wez/halfdeck/case/left-case.scad

module quarter(x, y, z, y_cut_delta=0, x_cut_delta=0, offset=[0,0,0], piece) {
    tongue_size = 2.8;
    displacement = 12;
    // tolerance on the groove side
    kerf = 0.25;

    y_cut = (y / 2) + y_cut_delta;
    x_cut = (x / 2) + x_cut_delta;
    total_z = z * 2;

    module cutout(kerf=0) {
        rotate([90, 0, 0])
        cylinder(h=kerf + max(y + abs(y_cut_delta),
                              x + abs(x_cut_delta))/2,
                 r=tongue_size, $fn=4);
    }

    module tongue() {
        cutout();
    }

    module groove() {
        cutout(kerf);
    }

    module top_left_quadrant() {
        cube([x_cut, y_cut, total_z]);
    }

    module offset_top_right() {
        translate([x_cut, 0, 0]) children();
    }

    module top_right_quadrant() {
        offset_top_right()
        cube([x - x_cut, y_cut, total_z]);
    }

    module offset_bottom_left() {
        translate([0, y_cut, 0]) children();
    }

    module bottom_left_quadrant() {
        offset_bottom_left()
        cube([x_cut, y - y_cut, total_z]);
    }

    module offset_bottom_right() {
        translate([x_cut, y_cut, 0]) children();
    }

    module bottom_right_quadrant() {
        offset_bottom_right()
        cube([x - x_cut, y - y_cut, total_z]);
    }

    module offset_top_left_lr() {
      offset_top_right()
      translate([0, y_cut, z/2])
      children();
    }

    module offset_bottom_left_lr() {
      offset_bottom_left()
      translate([x - x_cut, y - y_cut, z/2])
      children();
    }

    module offset_top_left_ud() {
      translate([0, y_cut, z/2])
      rotate([0, 0, 90])
      children();
    }

    module offset_top_right_ud() {
      offset_bottom_right()
      translate([0, 0, z/2])
      rotate([0, 0, 90])
      children();
    }

    // top left quadrant
    if (piece == undef || piece == 0)
    translate([-displacement, -displacement, 0]) {
      intersection() {
        translate(offset) {
          difference() {
            union() {
              top_left_quadrant();
              // RHS tongue
              intersection() {
                top_right_quadrant();
                offset_top_left_lr() tongue();
              }
            }
            // bottom groove
            offset_top_left_ud() groove();
          }
        }
        children(0);
      }
    }

    // top right quadrant
    if (piece == undef || piece == 1)
    translate([displacement, -displacement, 0]) {
      intersection() {
        translate(offset) {
          difference() {
            union() {
              top_right_quadrant();
              // bottom tongue
              intersection() {
                bottom_right_quadrant();
                offset_top_right_ud() tongue();
              }
            }
            // LHS groove
            offset_top_left_lr() groove();
          }
        }
        children(0);
      }
    }

    // bottom right quadrant
    if (piece == undef || piece == 2)
    translate([displacement, displacement, 0]) {
      intersection() {
        translate(offset) {
          difference() {
            union() {
              bottom_right_quadrant();
              // LHS tongue
              intersection() {
                bottom_left_quadrant();
                offset_bottom_left_lr() tongue();
              }
            }
            // top groove
            offset_top_right_ud() groove();
          }
        }
        children(0);
      }
    }

    // bottom left quadrant
    if (piece == undef || piece == 3)
    translate([-displacement, displacement, 0]) {
      intersection() {
        translate(offset) {
          difference() {
            union() {
              bottom_left_quadrant();
              // top tongue
              intersection() {
                top_left_quadrant();
                offset_top_left_ud() tongue();
              }
            }
            // RHS groove
            offset_bottom_left_lr() groove();
          }
        }
        children(0);
      }
    }
}


module case_top() {
difference() {
difference() {
difference() {
union() {
union() {
union() {
union() {
linear_extrude(height=2.0) {
polygon([
  [119.9620436791635, -10.0],
  [119.88614853201763, -9.998847719777999],
  [53.880686985647216, -7.994126032720432],
  [53.646495296320076, -7.975973004726603],
  [-5.810086836473021, -0.5439002381274649],
  [-6.047487665291121, -0.5025204617148387],
  [-6.279801550623147, -0.4384759607689326],
  [-6.504869964194179, -0.3523618003068363],
  [-6.720601698525187, -0.2449781040489396],
  [-6.9249922972416, -0.11732262012514494],
  [-7.116142679340018, 0.029418549432351115],
  [-7.292276784366992, 0.19388196927341883],
  [-7.451758074560958, 0.3745395389945354],
  [-7.593104740628792, 0.569712691377185],
  [-7.71500346987358, 0.7775879886781831],
  [-7.816321648748018, 0.9962339720600868],
  [-7.896117886454252, 1.2236191076063734],
  [-7.953650761810862, 1.45763066217724],
  [-7.988385712116106, 1.69609433372233],
  [-8.0, 1.9367944536567043],
  [-8.000000000000002, 99.39375],
  [-7.999999999999999, 126.83538329329558],
  [-7.988630737664156, 127.07353671349598],
  [-7.954626358757477, 127.30952403072804],
  [-7.898296147043448, 127.54119884361772],
  [-7.820152448885596, 127.76645397478553],
  [-7.720906013247321, 127.98324063648849],
  [-7.601459527138758, 128.18958706518433],
  [-7.462899405308439, 128.38361645552916],
  [-7.306485908855863, 128.56356403069117],
  [-7.133641682640258, 128.72779309371944],
  [-6.945938815742489, 128.87480991397337],
  [-6.745084542670518, 129.00327731321514],
  [-6.532905715361807, 129.11202682779387],
  [-6.311332187216184, 129.2000693363015],
  [-6.082379260288182, 129.26660405603724],
  [-5.848129355288844, 129.31102582645462],
  [-5.610713071115836, 129.33293061334462],
  [143.51094867944454, 135.94330272112006],
  [143.7578335033689, 135.94204409706296],
  [144.00339029973705, 135.9164401876724],
  [144.2452242532848, 135.86674069743202],
  [144.48097685611515, 135.79343032519606],
  [144.70834890926406, 135.69722403711918],
  [144.9251229458497, 135.57906009388333],
  [145.1291848571225, 135.44009090022388],
  [145.3185445105055, 135.2816717659965],
  [145.49135515854522, 135.10534768839287],
  [145.6459314494865, 134.91283828421348],
  [145.78076586382062, 134.70602101914633],
  [145.89454341650796, 134.48691289761004],
  [145.98615448149076, 134.25765079173254],
  [146.05470561342344, 134.02047060130883],
  [165.9330438628631, 49.86597310114771],
  [165.98320454827606, 49.58055907861434],
  [166.00000000000003, 49.291257900909926],
  [166.0, -6.398002531138397],
  [165.98859115294965, -6.63656923766047],
  [165.95446874123138, -6.872958527329727],
  [165.89794420274623, -7.105012856746026],
  [165.81953344134553, -7.3306142480280165],
  [165.7199521181364, -7.5477036197617124],
  [165.60010911958736, -7.754299580396419],
  [165.46109826205074, -7.9485165125592525],
  [165.30418830841614, -8.128581783231304],
  [165.13081138801294, -8.29285192270683],
  [164.9425499254547, -8.439827624668856],
  [164.7411221977268, -8.56816743047434],
  [164.52836665133918, -8.676699972751353],
  [164.3062251226821, -8.764434666560037],
  [164.07672511473476, -8.830570750538252],
  [163.8419612918881, -8.874504595512704],
  [163.60407636178044, -8.895835213869276],
  [137.156137109102, -9.99783268273088],
  [137.05206074732155, -10.0],
  [119.9620436791635, -10.0],
  [127.08639692372063, 86.55199944613877],
  [145.84698461860322, 89.85999723069379],
  [142.5389868340482, 108.62058492557635],
  [139.23098904949316, 127.38117262045891],
  [120.4704013546106, 124.07317483590388],
  [101.70981365972804, 120.76517705134886],
  [105.01781144428307, 102.00458935646631],
  [108.32580922883807, 83.24400166158375],
  [127.08639692372063, 86.55199944613877],
  [127.08639692372063, 86.55199944613877],
  [130.39439470827566, 67.7914117512562],
  [149.15498240315824, 71.09940953581122],
  [145.84698461860322, 89.85999723069378],
  [127.08639692372063, 86.55199944613877],
  [114.30000000000001, 26.19375],
  [114.30000000000001, 7.143750000000001],
  [133.35000000000002, 7.143750000000001],
  [133.35000000000002, 26.19375],
  [133.35000000000002, 45.24375],
  [133.35000000000002, 45.243750000000006],
  [133.35000000000002, 64.29375],
  [114.30000000000001, 64.29375],
  [114.30000000000001, 45.243750000000006],
  [114.30000000000001, 45.24375],
  [114.30000000000001, 26.19375],
  [0.0, 26.19375],
  [0.0, 7.143750000000001],
  [19.05, 7.143750000000001],
  [38.1, 7.143750000000001],
  [38.1, 2.38125],
  [57.150000000000006, 2.38125],
  [57.150000000000006, 0.0],
  [76.2, 0.0],
  [76.2, 2.38125],
  [95.25, 2.38125],
  [95.25, 4.7625],
  [114.3, 4.7625],
  [114.3, 23.8125],
  [114.3, 42.8625],
  [95.25, 42.8625],
  [95.25, 42.862500000000004],
  [114.3, 42.862500000000004],
  [114.3, 61.9125],
  [114.3, 61.91250000000001],
  [114.3, 80.9625],
  [95.25, 80.9625],
  [95.25, 78.58125],
  [76.2, 78.58125],
  [76.2, 76.2],
  [57.150000000000006, 76.2],
  [57.150000000000006, 78.58125],
  [38.1, 78.58125],
  [38.1, 83.34375],
  [38.1, 102.39375],
  [57.150000000000006, 102.39375],
  [57.150000000000006, 121.44375],
  [38.1, 121.44375],
  [19.05, 121.44375],
  [0.0, 121.44375],
  [0.0, 102.39375],
  [19.05, 102.39375],
  [19.05, 83.34375],
  [0.0, 83.34375],
  [0.0, 64.29375],
  [0.0, 45.243750000000006],
  [0.0, 45.24375],
  [0.0, 26.19375]
  ], [
  [
  0,
  1,
  2,
  3,
  4,
  5,
  6,
  7,
  8,
  9,
  10,
  11,
  12,
  13,
  14,
  15,
  16,
  17,
  18,
  19,
  20,
  21,
  22,
  23,
  24,
  25,
  26,
  27,
  28,
  29,
  30,
  31,
  32,
  33,
  34,
  35,
  36,
  37,
  38,
  39,
  40,
  41,
  42,
  43,
  44,
  45,
  46,
  47,
  48,
  49,
  50,
  51,
  52,
  53,
  54,
  55,
  56,
  57,
  58,
  59,
  60,
  61,
  62,
  63,
  64,
  65,
  66,
  67,
  68,
  69,
  70,
  71,
  72,
  73,
  74,
  75
  ],
  [
  76,
  77,
  78,
  79,
  80,
  81,
  82,
  83,
  84
  ],
  [
  85,
  86,
  87,
  88,
  89
  ],
  [
  90,
  91,
  92,
  93,
  94,
  95,
  96,
  97,
  98,
  99,
  100
  ],
  [
  101,
  102,
  103,
  104,
  105,
  106,
  107,
  108,
  109,
  110,
  111,
  112,
  113,
  114,
  115,
  116,
  117,
  118,
  119,
  120,
  121,
  122,
  123,
  124,
  125,
  126,
  127,
  128,
  129,
  130,
  131,
  132,
  133,
  134,
  135,
  136,
  137,
  138,
  139,
  140,
  141,
  142
  ]
  ]);

}
translate(v=[0, 0, 1.0]) {
linear_extrude(height=11.4) {
union() {
union() {
union() {
union() {
union() {
union() {
union() {
polygon([
  [56.956582132793095, -5.495278312942434],
  [56.94213631280969, -5.789329733931115],
  [56.898937974002784, -6.0805492789908175],
  [56.82740313998972, -6.36613234470582],
  [56.72822073032695, -6.643328610037702],
  [56.60234592583816, -6.909468523420426],
  [56.45099096970073, -7.161989012001239],
  [56.275613492881305, -7.398458165433368],
  [56.07790247635274, -7.616598656502074],
  [55.85976198528403, -7.8143096730306425],
  [55.623292831851906, -7.9896871498500674],
  [55.37077234327109, -8.141042105987497],
  [55.10463242988837, -8.266916910476294],
  [54.82743616455649, -8.366099320139059],
  [54.541853098841486, -8.437634154152125],
  [54.25063355378178, -8.480832492959024],
  [53.9565821327931, -8.495278312942434],
  [53.662530711804415, -8.480832492959024],
  [53.37131116674472, -8.437634154152125],
  [53.085728101029716, -8.366099320139062],
  [52.808531835697835, -8.266916910476297],
  [52.542391922315105, -8.141042105987502],
  [52.28987143373429, -7.989687149850073],
  [52.053402280302166, -7.814309673030648],
  [51.835261789233456, -7.61659865650208],
  [51.637550772704884, -7.398458165433374],
  [51.462173295885464, -7.161989012001245],
  [51.31081833974803, -6.909468523420431],
  [51.18494353525924, -6.643328610037707],
  [51.08576112559647, -6.366132344705825],
  [51.014226291583405, -6.080549278990822],
  [50.9710279527765, -5.789329733931119],
  [50.956582132793095, -5.495278312942436],
  [50.9710279527765, -5.2012268919537545],
  [51.014226291583405, -4.9100073468940515],
  [51.08576112559647, -4.624424281179048],
  [51.18494353525924, -4.347228015847166],
  [51.31081833974803, -4.081088102464442],
  [51.46217329588546, -3.828567613883628],
  [51.637550772704884, -3.592098460451498],
  [51.83526178923345, -3.3739579693827912],
  [52.05340228030216, -3.176246952854224],
  [52.289871433734284, -3.0008694760347994],
  [52.5423919223151, -2.84951451989737],
  [52.80853183569782, -2.723639715408575],
  [53.0857281010297, -2.6244573057458087],
  [53.371311166744704, -2.5529224717327437],
  [53.66253071180441, -2.509724132925844],
  [53.95658213279309, -2.4952783129424336],
  [54.25063355378177, -2.509724132925842],
  [54.54185309884147, -2.5529224717327406],
  [54.827436164556474, -2.624457305745804],
  [55.104632429888355, -2.7236397154085683],
  [55.37077234327108, -2.849514519897362],
  [55.62329283185189, -3.00086947603479],
  [55.85976198528402, -3.176246952854213],
  [56.077902476352726, -3.3739579693827793],
  [56.27561349288129, -3.5920984604514836],
  [56.45099096970072, -3.8285676138836116],
  [56.60234592583815, -4.081088102464424],
  [56.728220730326946, -4.347228015847145],
  [56.82740313998971, -4.624424281179026],
  [56.898937974002784, -4.910007346894027],
  [56.94213631280968, -5.201226891953728],
  [56.956582132793095, -5.495278312942409],
  [56.956582132793095, -5.495278312942434]
  ], [
  [
  0,
  1,
  2,
  3,
  4,
  5,
  6,
  7,
  8,
  9,
  10,
  11,
  12,
  13,
  14,
  15,
  16,
  17,
  18,
  19,
  20,
  21,
  22,
  23,
  24,
  25,
  26,
  27,
  28,
  29,
  30,
  31,
  32,
  33,
  34,
  35,
  36,
  37,
  38,
  39,
  40,
  41,
  42,
  43,
  44,
  45,
  46,
  47,
  48,
  49,
  50,
  51,
  52,
  53,
  54,
  55,
  56,
  57,
  58,
  59,
  60,
  61,
  62,
  63,
  64,
  65
  ]
  ]);

polygon([
  [-2.5, 1.9367944536567043],
  [-2.5144458199834094, 1.6427430326680228],
  [-2.5576441587903083, 1.3515234876083202],
  [-2.6291789928033733, 1.065940421893318],
  [-2.728361402466139, 0.7887441565614361],
  [-2.8542362069549343, 0.5226042431787128],
  [-3.0055911630923635, 0.27008375459789913],
  [-3.1809686399117876, 0.03361460116576942],
  [-3.3786796564403554, -0.18452588990293628],
  [-3.596820147509061, -0.38223690643150454],
  [-3.833289300941191, -0.5576143832509295],
  [-4.0858097895220045, -0.7089693393883592],
  [-4.351949702904728, -0.8348441438771548],
  [-4.629145968236609, -0.934026553539921],
  [-4.914729033951611, -1.005561387552986],
  [-5.205948579011314, -1.0487597263598858],
  [-5.499999999999996, -1.0632055463432957],
  [-5.794051420988676, -1.0487597263598867],
  [-6.0852709660483795, -1.0055613875529879],
  [-6.370854031763382, -0.9340265535399237],
  [-6.6480502970952635, -0.8348441438771583],
  [-6.914190210477987, -0.708969339388364],
  [-7.166710699058802, -0.5576143832509348],
  [-7.403179852490932, -0.3822369064315103],
  [-7.621320343559638, -0.18452588990294205],
  [-7.819031360088207, 0.03361460116576387],
  [-7.994408836907633, 0.27008375459789336],
  [-8.145763793045063, 0.5226042431787072],
  [-8.271638597533858, 0.788744156561431],
  [-8.370821007196625, 1.0659404218933133],
  [-8.44235584120969, 1.351523487608316],
  [-8.48555418001659, 1.6427430326680192],
  [-8.5, 1.9367944536567012],
  [-8.48555418001659, 2.230845874645383],
  [-8.442355841209693, 2.5220654197050867],
  [-8.370821007196627, 2.8076484854200894],
  [-8.271638597533862, 3.084844750751972],
  [-8.145763793045067, 3.350984664134696],
  [-7.9944088369076365, 3.60350515271551],
  [-7.8190313600882115, 3.8399743061476403],
  [-7.621320343559643, 4.058114797216347],
  [-7.403179852490938, 4.255825813744914],
  [-7.166710699058809, 4.431203290564339],
  [-6.9141902104779955, 4.582558246701768],
  [-6.648050297095273, 4.708433051190563],
  [-6.370854031763392, 4.807615460853329],
  [-6.085270966048391, 4.8791502948663945],
  [-5.794051420988689, 4.922348633673294],
  [-5.500000000000009, 4.936794453656704],
  [-5.205948579011328, 4.922348633673296],
  [-4.914729033951626, 4.879150294866397],
  [-4.6291459682366245, 4.807615460853334],
  [-4.351949702904742, 4.708433051190569],
  [-4.085809789522019, 4.582558246701776],
  [-3.8332893009412055, 4.431203290564348],
  [-3.5968201475090753, 4.2558258137449245],
  [-3.378679656440369, 4.0581147972163585],
  [-3.1809686399118005, 3.8399743061476546],
  [-3.0055911630923746, 3.6035051527155266],
  [-2.854236206954944, 3.3509846641347147],
  [-2.728361402466148, 3.0848447507519925],
  [-2.62917899280338, 2.807648485420112],
  [-2.557644158790313, 2.522065419705111],
  [-2.5144458199834117, 2.23084587464541],
  [-2.5, 1.936794453656729],
  [-2.5, 1.9367944536567043]
  ], [
  [
  0,
  1,
  2,
  3,
  4,
  5,
  6,
  7,
  8,
  9,
  10,
  11,
  12,
  13,
  14,
  15,
  16,
  17,
  18,
  19,
  20,
  21,
  22,
  23,
  24,
  25,
  26,
  27,
  28,
  29,
  30,
  31,
  32,
  33,
  34,
  35,
  36,
  37,
  38,
  39,
  40,
  41,
  42,
  43,
  44,
  45,
  46,
  47,
  48,
  49,
  50,
  51,
  52,
  53,
  54,
  55,
  56,
  57,
  58,
  59,
  60,
  61,
  62,
  63,
  64,
  65
  ]
  ]);

}
polygon([
  [-2.5, 64.38608887347614],
  [-2.5144458199834094, 64.09203745248746],
  [-2.5576441587903083, 63.800817907427756],
  [-2.6291789928033733, 63.515234841712754],
  [-2.728361402466139, 63.23803857638087],
  [-2.8542362069549343, 62.97189866299815],
  [-3.0055911630923635, 62.719378174417336],
  [-3.1809686399117876, 62.482909020985204],
  [-3.3786796564403554, 62.2647685299165],
  [-3.596820147509061, 62.06705751338793],
  [-3.833289300941191, 61.89168003656851],
  [-4.0858097895220045, 61.74032508043108],
  [-4.351949702904728, 61.61445027594228],
  [-4.629145968236609, 61.515267866279515],
  [-4.914729033951611, 61.44373303226645],
  [-5.205948579011314, 61.40053469345955],
  [-5.499999999999996, 61.38608887347614],
  [-5.794051420988676, 61.40053469345955],
  [-6.0852709660483795, 61.44373303226645],
  [-6.370854031763382, 61.515267866279515],
  [-6.6480502970952635, 61.614450275942275],
  [-6.914190210477987, 61.74032508043107],
  [-7.166710699058802, 61.8916800365685],
  [-7.403179852490932, 62.06705751338792],
  [-7.621320343559638, 62.264768529916495],
  [-7.819031360088207, 62.4829090209852],
  [-7.994408836907633, 62.71937817441733],
  [-8.145763793045063, 62.97189866299814],
  [-8.271638597533858, 63.238038576380866],
  [-8.370821007196625, 63.51523484171275],
  [-8.44235584120969, 63.80081790742775],
  [-8.48555418001659, 64.09203745248746],
  [-8.5, 64.38608887347614],
  [-8.48555418001659, 64.68014029446482],
  [-8.442355841209693, 64.97135983952452],
  [-8.370821007196627, 65.25694290523953],
  [-8.271638597533862, 65.53413917057141],
  [-8.145763793045067, 65.80027908395414],
  [-7.9944088369076365, 66.05279957253495],
  [-7.8190313600882115, 66.28926872596708],
  [-7.621320343559643, 66.50740921703579],
  [-7.403179852490938, 66.70512023356434],
  [-7.166710699058809, 66.88049771038378],
  [-6.9141902104779955, 67.0318526665212],
  [-6.648050297095273, 67.15772747101],
  [-6.370854031763392, 67.25690988067277],
  [-6.085270966048391, 67.32844471468583],
  [-5.794051420988689, 67.37164305349273],
  [-5.500000000000009, 67.38608887347614],
  [-5.205948579011328, 67.37164305349273],
  [-4.914729033951626, 67.32844471468583],
  [-4.6291459682366245, 67.25690988067277],
  [-4.351949702904742, 67.15772747101],
  [-4.085809789522019, 67.03185266652122],
  [-3.8332893009412055, 66.88049771038378],
  [-3.5968201475090753, 66.70512023356436],
  [-3.378679656440369, 66.5074092170358],
  [-3.1809686399118005, 66.28926872596709],
  [-3.0055911630923746, 66.05279957253497],
  [-2.854236206954944, 65.80027908395415],
  [-2.728361402466148, 65.53413917057142],
  [-2.62917899280338, 65.25694290523955],
  [-2.557644158790313, 64.97135983952455],
  [-2.5144458199834117, 64.68014029446485],
  [-2.5, 64.38608887347617],
  [-2.5, 64.38608887347614]
  ], [
  [
  0,
  1,
  2,
  3,
  4,
  5,
  6,
  7,
  8,
  9,
  10,
  11,
  12,
  13,
  14,
  15,
  16,
  17,
  18,
  19,
  20,
  21,
  22,
  23,
  24,
  25,
  26,
  27,
  28,
  29,
  30,
  31,
  32,
  33,
  34,
  35,
  36,
  37,
  38,
  39,
  40,
  41,
  42,
  43,
  44,
  45,
  46,
  47,
  48,
  49,
  50,
  51,
  52,
  53,
  54,
  55,
  56,
  57,
  58,
  59,
  60,
  61,
  62,
  63,
  64,
  65
  ]
  ]);

}
polygon([
  [-2.499999999999999, 126.83538329329558],
  [-2.5144458199834085, 126.5413318723069],
  [-2.5576441587903074, 126.2501123272472],
  [-2.6291789928033724, 125.96452926153219],
  [-2.7283614024661382, 125.68733299620031],
  [-2.8542362069549334, 125.42119308281758],
  [-3.0055911630923626, 125.16867259423677],
  [-3.1809686399117867, 124.93220344080464],
  [-3.3786796564403545, 124.71406294973593],
  [-3.59682014750906, 124.51635193320737],
  [-3.83328930094119, 124.34097445638794],
  [-4.085809789522004, 124.18961950025052],
  [-4.351949702904727, 124.06374469576171],
  [-4.6291459682366085, 123.96456228609895],
  [-4.91472903395161, 123.89302745208589],
  [-5.205948579011313, 123.84982911327899],
  [-5.499999999999995, 123.83538329329558],
  [-5.7940514209886755, 123.84982911327899],
  [-6.085270966048379, 123.89302745208589],
  [-6.370854031763381, 123.96456228609895],
  [-6.648050297095263, 124.06374469576171],
  [-6.914190210477987, 124.18961950025052],
  [-7.1667106990588, 124.34097445638794],
  [-7.403179852490931, 124.51635193320736],
  [-7.621320343559638, 124.71406294973593],
  [-7.819031360088207, 124.93220344080464],
  [-7.994408836907632, 125.16867259423677],
  [-8.145763793045063, 125.42119308281758],
  [-8.271638597533858, 125.68733299620031],
  [-8.370821007196625, 125.96452926153219],
  [-8.44235584120969, 126.2501123272472],
  [-8.485554180016589, 126.5413318723069],
  [-8.5, 126.83538329329558],
  [-8.485554180016589, 127.12943471428426],
  [-8.442355841209691, 127.42065425934396],
  [-8.370821007196627, 127.70623732505896],
  [-8.27163859753386, 127.98343359039085],
  [-8.145763793045065, 128.24957350377358],
  [-7.994408836907636, 128.5020939923544],
  [-7.819031360088211, 128.73856314578651],
  [-7.621320343559642, 128.95670363685522],
  [-7.403179852490937, 129.15441465338378],
  [-7.166710699058807, 129.3297921302032],
  [-6.9141902104779955, 129.48114708634066],
  [-6.648050297095272, 129.60702189082943],
  [-6.3708540317633915, 129.7062043004922],
  [-6.08527096604839, 129.77773913450528],
  [-5.794051420988689, 129.82093747331217],
  [-5.500000000000008, 129.8353832932956],
  [-5.205948579011327, 129.82093747331217],
  [-4.914729033951625, 129.77773913450528],
  [-4.629145968236623, 129.7062043004922],
  [-4.351949702904742, 129.60702189082946],
  [-4.085809789522019, 129.48114708634066],
  [-3.8332893009412046, 129.32979213020323],
  [-3.5968201475090744, 129.1544146533838],
  [-3.3786796564403683, 128.95670363685522],
  [-3.1809686399117996, 128.73856314578651],
  [-3.0055911630923737, 128.5020939923544],
  [-2.854236206954943, 128.24957350377358],
  [-2.728361402466147, 127.98343359039086],
  [-2.629178992803379, 127.70623732505899],
  [-2.5576441587903123, 127.42065425934399],
  [-2.5144458199834108, 127.12943471428429],
  [-2.499999999999999, 126.8353832932956],
  [-2.499999999999999, 126.83538329329558]
  ], [
  [
  0,
  1,
  2,
  3,
  4,
  5,
  6,
  7,
  8,
  9,
  10,
  11,
  12,
  13,
  14,
  15,
  16,
  17,
  18,
  19,
  20,
  21,
  22,
  23,
  24,
  25,
  26,
  27,
  28,
  29,
  30,
  31,
  32,
  33,
  34,
  35,
  36,
  37,
  38,
  39,
  40,
  41,
  42,
  43,
  44,
  45,
  46,
  47,
  48,
  49,
  50,
  51,
  52,
  53,
  54,
  55,
  56,
  57,
  58,
  59,
  60,
  61,
  62,
  63,
  64,
  65
  ]
  ]);

}
polygon([
  [72.06083087528019, 130.14056934718332],
  [72.04638505529678, 129.84651792619462],
  [72.00318671648988, 129.55529838113492],
  [71.93165188247681, 129.26971531541992],
  [71.83246947281405, 128.99251905008805],
  [71.70659466832525, 128.72637913670533],
  [71.55523971218783, 128.47385864812452],
  [71.3798622353684, 128.2373894946924],
  [71.18215121883983, 128.01924900362368],
  [70.96401072777113, 127.82153798709511],
  [70.727541574339, 127.64616051027568],
  [70.47502108575819, 127.49480555413825],
  [70.20888117237546, 127.36893074964945],
  [69.93168490704358, 127.26974833998669],
  [69.64610184132857, 127.19821350597363],
  [69.35488229626887, 127.15501516716672],
  [69.06083087528019, 127.14056934718332],
  [68.76677945429151, 127.15501516716672],
  [68.4755599092318, 127.19821350597363],
  [68.1899768435168, 127.26974833998669],
  [67.91278057818492, 127.36893074964945],
  [67.6466406648022, 127.49480555413825],
  [67.39412017622139, 127.64616051027568],
  [67.15765102278925, 127.8215379870951],
  [66.93951053172054, 128.01924900362366],
  [66.74179951519199, 128.23738949469237],
  [66.56642203837255, 128.47385864812452],
  [66.41506708223513, 128.72637913670533],
  [66.28919227774632, 128.99251905008805],
  [66.19000986808356, 129.26971531541992],
  [66.1184750340705, 129.55529838113492],
  [66.0752766952636, 129.84651792619462],
  [66.06083087528019, 130.14056934718332],
  [66.0752766952636, 130.43462076817198],
  [66.1184750340705, 130.72584031323169],
  [66.19000986808356, 131.0114233789467],
  [66.28919227774632, 131.28861964427858],
  [66.41506708223513, 131.5547595576613],
  [66.56642203837255, 131.8072800462421],
  [66.74179951519197, 132.04374919967424],
  [66.93951053172054, 132.26188969074295],
  [67.15765102278925, 132.45960070727153],
  [67.39412017622138, 132.63497818409095],
  [67.64664066480219, 132.78633314022838],
  [67.91278057818492, 132.91220794471718],
  [68.1899768435168, 133.01139035437996],
  [68.47555990923179, 133.082925188393],
  [68.7667794542915, 133.1261235271999],
  [69.06083087528017, 133.14056934718332],
  [69.35488229626885, 133.1261235271999],
  [69.64610184132856, 133.082925188393],
  [69.93168490704356, 133.01139035437996],
  [70.20888117237544, 132.91220794471718],
  [70.47502108575817, 132.78633314022838],
  [70.72754157433899, 132.63497818409095],
  [70.96401072777111, 132.45960070727153],
  [71.18215121883982, 132.26188969074298],
  [71.37986223536839, 132.04374919967427],
  [71.55523971218781, 131.80728004624214],
  [71.70659466832524, 131.55475955766133],
  [71.83246947281404, 131.2886196442786],
  [71.93165188247681, 131.01142337894672],
  [72.00318671648988, 130.7258403132317],
  [72.04638505529678, 130.434620768172],
  [72.06083087528019, 130.14056934718334],
  [72.06083087528019, 130.14056934718332]
  ], [
  [
  0,
  1,
  2,
  3,
  4,
  5,
  6,
  7,
  8,
  9,
  10,
  11,
  12,
  13,
  14,
  15,
  16,
  17,
  18,
  19,
  20,
  21,
  22,
  23,
  24,
  25,
  26,
  27,
  28,
  29,
  30,
  31,
  32,
  33,
  34,
  35,
  36,
  37,
  38,
  39,
  40,
  41,
  42,
  43,
  44,
  45,
  46,
  47,
  48,
  49,
  50,
  51,
  52,
  53,
  54,
  55,
  56,
  57,
  58,
  59,
  60,
  61,
  62,
  63,
  64,
  65
  ]
  ]);

}
polygon([
  [146.62166175056038, 133.44575540107104],
  [146.60721593057696, 133.15170398008235],
  [146.56401759177007, 132.86048443502264],
  [146.49248275775702, 132.57490136930764],
  [146.39330034809424, 132.29770510397577],
  [146.26742554360544, 132.03156519059306],
  [146.11607058746802, 131.77904470201224],
  [145.9406931106486, 131.54257554858012],
  [145.74298209412, 131.3244350575114],
  [145.52484160305133, 131.12672404098282],
  [145.28837244961917, 130.9513465641634],
  [145.03585196103836, 130.79999160802598],
  [144.76971204765564, 130.67411680353717],
  [144.49251578232378, 130.5749343938744],
  [144.20693271660878, 130.50339955986135],
  [143.91571317154907, 130.46020122105446],
  [143.62166175056038, 130.44575540107104],
  [143.3276103295717, 130.46020122105446],
  [143.036390784512, 130.50339955986135],
  [142.750807718797, 130.5749343938744],
  [142.4736114534651, 130.67411680353717],
  [142.2074715400824, 130.79999160802598],
  [141.95495105150158, 130.9513465641634],
  [141.71848189806946, 131.12672404098282],
  [141.50034140700075, 131.32443505751138],
  [141.30263039047216, 131.5425755485801],
  [141.12725291365274, 131.77904470201224],
  [140.97589795751531, 132.03156519059306],
  [140.8500231530265, 132.29770510397577],
  [140.75084074336374, 132.57490136930764],
  [140.6793059093507, 132.86048443502264],
  [140.6361075705438, 133.15170398008235],
  [140.62166175056038, 133.44575540107104],
  [140.6361075705438, 133.7398068220597],
  [140.6793059093507, 134.0310263671194],
  [140.75084074336374, 134.3166094328344],
  [140.8500231530265, 134.5938056981663],
  [140.97589795751531, 134.85994561154902],
  [141.12725291365274, 135.11246610012984],
  [141.30263039047216, 135.34893525356196],
  [141.50034140700075, 135.56707574463067],
  [141.71848189806943, 135.76478676115926],
  [141.95495105150158, 135.94016423797868],
  [142.2074715400824, 136.0915191941161],
  [142.4736114534651, 136.2173939986049],
  [142.75080771879698, 136.31657640826768],
  [143.03639078451198, 136.38811124228073],
  [143.32761032957168, 136.43130958108762],
  [143.62166175056038, 136.44575540107104],
  [143.91571317154904, 136.43130958108762],
  [144.20693271660875, 136.38811124228073],
  [144.49251578232375, 136.31657640826768],
  [144.76971204765564, 136.2173939986049],
  [145.03585196103836, 136.0915191941161],
  [145.28837244961917, 135.94016423797868],
  [145.5248416030513, 135.76478676115926],
  [145.74298209412, 135.5670757446307],
  [145.94069311064857, 135.348935253562],
  [146.11607058746802, 135.11246610012986],
  [146.26742554360544, 134.85994561154905],
  [146.39330034809424, 134.59380569816634],
  [146.492482757757, 134.31660943283444],
  [146.56401759177007, 134.03102636711944],
  [146.60721593057696, 133.73980682205973],
  [146.62166175056038, 133.44575540107107],
  [146.62166175056038, 133.44575540107104]
  ], [
  [
  0,
  1,
  2,
  3,
  4,
  5,
  6,
  7,
  8,
  9,
  10,
  11,
  12,
  13,
  14,
  15,
  16,
  17,
  18,
  19,
  20,
  21,
  22,
  23,
  24,
  25,
  26,
  27,
  28,
  29,
  30,
  31,
  32,
  33,
  34,
  35,
  36,
  37,
  38,
  39,
  40,
  41,
  42,
  43,
  44,
  45,
  46,
  47,
  48,
  49,
  50,
  51,
  52,
  53,
  54,
  55,
  56,
  57,
  58,
  59,
  60,
  61,
  62,
  63,
  64,
  65
  ]
  ]);

}
polygon([
  [166.50000000000003, 49.291257900909926],
  [166.4855541800166, 48.997206479921246],
  [166.44235584120972, 48.70598693486154],
  [166.37082100719667, 48.42040386914654],
  [166.2716385975339, 48.14320760381466],
  [166.1457637930451, 47.877067690431936],
  [165.99440883690767, 47.62454720185112],
  [165.81903136008825, 47.38807804841899],
  [165.62132034355966, 47.16993755735029],
  [165.40317985249098, 46.972226540821715],
  [165.16671069905883, 46.796849064002295],
  [164.914190210478, 46.64549410786486],
  [164.6480502970953, 46.51961930337607],
  [164.37085403176343, 46.4204368937133],
  [164.08527096604843, 46.34890205970024],
  [163.79405142098872, 46.305703720893334],
  [163.50000000000003, 46.291257900909926],
  [163.20594857901136, 46.305703720893334],
  [162.91472903395166, 46.34890205970024],
  [162.62914596823666, 46.4204368937133],
  [162.35194970290476, 46.51961930337606],
  [162.08580978952205, 46.645494107864856],
  [161.83328930094123, 46.79684906400229],
  [161.5968201475091, 46.97222654082171],
  [161.3786796564404, 47.16993755735028],
  [161.1809686399118, 47.38807804841898],
  [161.0055911630924, 47.624547201851115],
  [160.85423620695497, 47.87706769043193],
  [160.72836140246616, 48.14320760381465],
  [160.6291789928034, 48.42040386914653],
  [160.55764415879034, 48.705986934861535],
  [160.51444581998345, 48.99720647992124],
  [160.50000000000003, 49.291257900909926],
  [160.51444581998345, 49.585309321898606],
  [160.55764415879034, 49.87652886695831],
  [160.6291789928034, 50.16211193267331],
  [160.72836140246616, 50.43930819800519],
  [160.85423620695497, 50.705448111387916],
  [161.0055911630924, 50.95796859996873],
  [161.1809686399118, 51.19443775340086],
  [161.3786796564404, 51.41257824446957],
  [161.59682014750908, 51.61028926099814],
  [161.83328930094123, 51.78566673781756],
  [162.08580978952205, 51.93702169395499],
  [162.35194970290476, 52.062896498443784],
  [162.62914596823663, 52.16207890810655],
  [162.91472903395163, 52.233613742119616],
  [163.20594857901133, 52.27681208092652],
  [163.50000000000003, 52.291257900909926],
  [163.7940514209887, 52.27681208092652],
  [164.0852709660484, 52.233613742119616],
  [164.3708540317634, 52.16207890810656],
  [164.6480502970953, 52.06289649844379],
  [164.914190210478, 51.937021693954996],
  [165.16671069905883, 51.78566673781757],
  [165.40317985249095, 51.610289260998144],
  [165.62132034355966, 51.41257824446958],
  [165.81903136008822, 51.19443775340088],
  [165.99440883690767, 50.95796859996875],
  [166.1457637930451, 50.70544811138794],
  [166.2716385975339, 50.439308198005214],
  [166.37082100719664, 50.162111932673334],
  [166.44235584120972, 49.87652886695833],
  [166.4855541800166, 49.585309321898634],
  [166.50000000000003, 49.29125790090995],
  [166.50000000000003, 49.291257900909926]
  ], [
  [
  0,
  1,
  2,
  3,
  4,
  5,
  6,
  7,
  8,
  9,
  10,
  11,
  12,
  13,
  14,
  15,
  16,
  17,
  18,
  19,
  20,
  21,
  22,
  23,
  24,
  25,
  26,
  27,
  28,
  29,
  30,
  31,
  32,
  33,
  34,
  35,
  36,
  37,
  38,
  39,
  40,
  41,
  42,
  43,
  44,
  45,
  46,
  47,
  48,
  49,
  50,
  51,
  52,
  53,
  54,
  55,
  56,
  57,
  58,
  59,
  60,
  61,
  62,
  63,
  64,
  65
  ]
  ]);

}
polygon([
  [166.5, -6.398002531138396],
  [166.48555418001658, -6.692053952127078],
  [166.4423558412097, -6.98327349718678],
  [166.37082100719664, -7.2688565629017825],
  [166.27163859753387, -7.546052828233664],
  [166.14576379304506, -7.812192741616387],
  [165.99440883690764, -8.064713230197201],
  [165.81903136008822, -8.301182383629332],
  [165.62132034355963, -8.519322874698037],
  [165.40317985249095, -8.717033891226606],
  [165.1667106990588, -8.89241136804603],
  [164.91419021047798, -9.04376632418346],
  [164.64805029709527, -9.169641128672255],
  [164.3708540317634, -9.268823538335022],
  [164.0852709660484, -9.340358372348087],
  [163.7940514209887, -9.383556711154986],
  [163.5, -9.398002531138395],
  [163.20594857901133, -9.383556711154988],
  [162.91472903395163, -9.340358372348089],
  [162.62914596823663, -9.268823538335024],
  [162.35194970290473, -9.169641128672259],
  [162.08580978952202, -9.043766324183466],
  [161.8332893009412, -8.892411368046035],
  [161.59682014750908, -8.717033891226611],
  [161.37867965644037, -8.519322874698043],
  [161.18096863991178, -8.301182383629337],
  [161.00559116309236, -8.064713230197206],
  [160.85423620695494, -7.812192741616394],
  [160.72836140246613, -7.54605282823367],
  [160.62917899280336, -7.268856562901787],
  [160.5576441587903, -6.983273497186785],
  [160.51444581998342, -6.692053952127082],
  [160.5, -6.398002531138399],
  [160.51444581998342, -6.103951110149717],
  [160.5576441587903, -5.812731565090014],
  [160.62917899280336, -5.527148499375011],
  [160.72836140246613, -5.249952234043128],
  [160.85423620695494, -4.983812320660404],
  [161.00559116309236, -4.731291832079591],
  [161.18096863991178, -4.494822678647461],
  [161.37867965644037, -4.2766821875787535],
  [161.59682014750905, -4.078971171050187],
  [161.8332893009412, -3.903593694230762],
  [162.08580978952202, -3.752238738093333],
  [162.35194970290473, -3.6263639336045377],
  [162.6291459682366, -3.5271815239417714],
  [162.9147290339516, -3.4556466899287064],
  [163.2059485790113, -3.4124483511218067],
  [163.5, -3.3980025311383963],
  [163.79405142098867, -3.412448351121805],
  [164.08527096604837, -3.4556466899287033],
  [164.37085403176337, -3.5271815239417665],
  [164.64805029709527, -3.626363933604531],
  [164.91419021047798, -3.752238738093325],
  [165.1667106990588, -3.9035936942307528],
  [165.40317985249092, -4.078971171050176],
  [165.62132034355963, -4.276682187578742],
  [165.8190313600882, -4.494822678647447],
  [165.99440883690764, -4.731291832079574],
  [166.14576379304506, -4.983812320660386],
  [166.27163859753387, -5.249952234043108],
  [166.3708210071966, -5.527148499374989],
  [166.4423558412097, -5.812731565089989],
  [166.48555418001658, -6.103951110149691],
  [166.5, -6.3980025311383715],
  [166.5, -6.398002531138396]
  ], [
  [
  0,
  1,
  2,
  3,
  4,
  5,
  6,
  7,
  8,
  9,
  10,
  11,
  12,
  13,
  14,
  15,
  16,
  17,
  18,
  19,
  20,
  21,
  22,
  23,
  24,
  25,
  26,
  27,
  28,
  29,
  30,
  31,
  32,
  33,
  34,
  35,
  36,
  37,
  38,
  39,
  40,
  41,
  42,
  43,
  44,
  45,
  46,
  47,
  48,
  49,
  50,
  51,
  52,
  53,
  54,
  55,
  56,
  57,
  58,
  59,
  60,
  61,
  62,
  63,
  64,
  65
  ]
  ]);

}
}
}
}
translate(v=[0, 0, 1.0]) {
linear_extrude(height=11.4) {
polygon([
  [119.9620436791635, -10.0],
  [119.88614853201763, -9.998847719777999],
  [53.880686985647216, -7.994126032720432],
  [53.646495296320076, -7.975973004726603],
  [-5.810086836473021, -0.5439002381274649],
  [-6.047487665291121, -0.5025204617148387],
  [-6.279801550623147, -0.4384759607689326],
  [-6.504869964194179, -0.3523618003068363],
  [-6.720601698525187, -0.2449781040489396],
  [-6.9249922972416, -0.11732262012514494],
  [-7.116142679340018, 0.029418549432351115],
  [-7.292276784366992, 0.19388196927341883],
  [-7.451758074560958, 0.3745395389945354],
  [-7.593104740628792, 0.569712691377185],
  [-7.71500346987358, 0.7775879886781831],
  [-7.816321648748018, 0.9962339720600868],
  [-7.896117886454252, 1.2236191076063734],
  [-7.953650761810862, 1.45763066217724],
  [-7.988385712116106, 1.69609433372233],
  [-8.0, 1.9367944536567043],
  [-8.000000000000002, 99.39375],
  [-7.999999999999999, 126.83538329329558],
  [-7.988630737664156, 127.07353671349598],
  [-7.954626358757477, 127.30952403072804],
  [-7.898296147043448, 127.54119884361772],
  [-7.820152448885596, 127.76645397478553],
  [-7.720906013247321, 127.98324063648849],
  [-7.601459527138758, 128.18958706518433],
  [-7.462899405308439, 128.38361645552916],
  [-7.306485908855863, 128.56356403069117],
  [-7.133641682640258, 128.72779309371944],
  [-6.945938815742489, 128.87480991397337],
  [-6.745084542670518, 129.00327731321514],
  [-6.532905715361807, 129.11202682779387],
  [-6.311332187216184, 129.2000693363015],
  [-6.082379260288182, 129.26660405603724],
  [-5.848129355288844, 129.31102582645462],
  [-5.610713071115836, 129.33293061334462],
  [143.51094867944454, 135.94330272112006],
  [143.7578335033689, 135.94204409706296],
  [144.00339029973705, 135.9164401876724],
  [144.2452242532848, 135.86674069743202],
  [144.48097685611515, 135.79343032519606],
  [144.70834890926406, 135.69722403711918],
  [144.9251229458497, 135.57906009388333],
  [145.1291848571225, 135.44009090022388],
  [145.3185445105055, 135.2816717659965],
  [145.49135515854522, 135.10534768839287],
  [145.6459314494865, 134.91283828421348],
  [145.78076586382062, 134.70602101914633],
  [145.89454341650796, 134.48691289761004],
  [145.98615448149076, 134.25765079173254],
  [146.05470561342344, 134.02047060130883],
  [165.9330438628631, 49.86597310114771],
  [165.98320454827606, 49.58055907861434],
  [166.00000000000003, 49.291257900909926],
  [166.0, -6.398002531138397],
  [165.98859115294965, -6.63656923766047],
  [165.95446874123138, -6.872958527329727],
  [165.89794420274623, -7.105012856746026],
  [165.81953344134553, -7.3306142480280165],
  [165.7199521181364, -7.5477036197617124],
  [165.60010911958736, -7.754299580396419],
  [165.46109826205074, -7.9485165125592525],
  [165.30418830841614, -8.128581783231304],
  [165.13081138801294, -8.29285192270683],
  [164.9425499254547, -8.439827624668856],
  [164.7411221977268, -8.56816743047434],
  [164.52836665133918, -8.676699972751353],
  [164.3062251226821, -8.764434666560037],
  [164.07672511473476, -8.830570750538252],
  [163.8419612918881, -8.874504595512704],
  [163.60407636178044, -8.895835213869276],
  [137.156137109102, -9.99783268273088],
  [137.05206074732155, -10.0],
  [119.9620436791635, -10.0],
  [119.97722533267093, -8.0],
  [137.03123870552528, -8.0],
  [137.0936800102856, -7.998699703604178],
  [163.47306155724934, -6.89955880581402],
  [163.5680796125103, -6.891038745830236],
  [163.61481773892984, -6.882292144349592],
  [163.66050791493169, -6.869125393968778],
  [163.70473312273197, -6.851658668640838],
  [163.74708971542574, -6.830051388523816],
  [163.78719110110234, -6.804500764941254],
  [163.8246712713019, -6.77524000041792],
  [163.85918814160075, -6.742536160223587],
  [163.89042667384345, -6.706687734847196],
  [163.91810175152142, -6.668021915649837],
  [163.94196078205152, -6.626891608565921],
  [163.96178600221003, -6.5836722131010355],
  [163.97739646567302, -6.538758196033744],
  [163.9886496945287, -6.492559491084399],
  [163.99544297968347, -6.44549775742044],
  [164.0, -6.350207381130173],
  [164.00000000000003, 49.233251487806584],
  [163.99329595692464, 49.348728438886354],
  [163.97327390564394, 49.462653799920496],
  [144.11962867495856, 133.51261396104692],
  [144.09225007809076, 133.607341219891],
  [144.07401737333777, 133.6529696413955],
  [144.0513730287268, 133.6965771869433],
  [144.02453788531312, 133.73773856993228],
  [143.9937736553036, 133.776052360185],
  [143.95938036968408, 133.8111448989343],
  [143.9216934521388, 133.84267394296535],
  [143.8810804478006, 133.87033200237371],
  [143.83793743873375, 133.8938493393883],
  [143.7926851811062, 133.91299659901478],
  [143.74576500172682, 133.92758704584077],
  [143.69763449396436, 133.9374783851904],
  [143.64876305502764, 133.9425741508659],
  [143.55015986823162, 133.9430768319989],
  [-5.47447735606841, 127.33700569709775],
  [-5.569308692124115, 127.32825625426139],
  [-5.615945249194452, 127.31941237263317],
  [-5.6615272367009, 127.30616604814004],
  [-5.705640067784389, 127.28863776153257],
  [-5.747882518166195, 127.26698693976158],
  [-5.787870375445877, 127.24141050592524],
  [-5.825239933671888, 127.21214108817216],
  [-5.859651301395607, 127.17944490385335],
  [-5.89079149312311, 127.14361933816667],
  [-5.918377276047581, 127.10499023931546],
  [-5.942157746166701, 127.06390895478668],
  [-5.961916610357738, 127.0207491357013],
  [-5.977474153652467, 126.97590333830348],
  [-5.988688873818028, 126.92977945350155],
  [-5.995458768377945, 126.88279699693256],
  [-5.999999999999999, 126.78767122616861],
  [-6.000000000000002, 99.39375],
  [-6.0, 1.985018507131056],
  [-5.9953610404178015, 1.88887846488582],
  [-5.98844638042828, 1.841407684185198],
  [-5.976993354936246, 1.7948231830053398],
  [-5.961108378929866, 1.749557797992357],
  [-5.940939046556629, 1.7060321093164077],
  [-5.916672759762629, 1.6646505328804122],
  [-5.88853498706042, 1.625797562717811],
  [-5.8567871686040585, 1.5898341984930942],
  [-5.821724287036152, 1.5570945912985803],
  [-5.783672126677123, 1.5278829389127728],
  [-5.74298424652302, 1.502470659367998],
  [-5.700038695176605, 1.48109386908857],
  [-5.655234498235245, 1.4639511890315748],
  [-5.608987950772275, 1.4512018992140334],
  [-5.514165705906545, 1.434674057626363],
  [53.84792295521751, -5.985587025014145],
  [53.98838622533089, -5.996474830989665],
  [119.93168999363454, -7.999308658424853],
  [119.97722533267093, -8.0]
  ], [
  [
  0,
  1,
  2,
  3,
  4,
  5,
  6,
  7,
  8,
  9,
  10,
  11,
  12,
  13,
  14,
  15,
  16,
  17,
  18,
  19,
  20,
  21,
  22,
  23,
  24,
  25,
  26,
  27,
  28,
  29,
  30,
  31,
  32,
  33,
  34,
  35,
  36,
  37,
  38,
  39,
  40,
  41,
  42,
  43,
  44,
  45,
  46,
  47,
  48,
  49,
  50,
  51,
  52,
  53,
  54,
  55,
  56,
  57,
  58,
  59,
  60,
  61,
  62,
  63,
  64,
  65,
  66,
  67,
  68,
  69,
  70,
  71,
  72,
  73,
  74,
  75
  ],
  [
  76,
  77,
  78,
  79,
  80,
  81,
  82,
  83,
  84,
  85,
  86,
  87,
  88,
  89,
  90,
  91,
  92,
  93,
  94,
  95,
  96,
  97,
  98,
  99,
  100,
  101,
  102,
  103,
  104,
  105,
  106,
  107,
  108,
  109,
  110,
  111,
  112,
  113,
  114,
  115,
  116,
  117,
  118,
  119,
  120,
  121,
  122,
  123,
  124,
  125,
  126,
  127,
  128,
  129,
  130,
  131,
  132,
  133,
  134,
  135,
  136,
  137,
  138,
  139,
  140,
  141,
  142,
  143,
  144,
  145,
  146,
  147,
  148,
  149,
  150,
  151
  ]
  ]);

}
}
}
translate(v=[0, 0, 1]) {
linear_extrude(height=11.4) {
polygon([
  [-2.0, 83.34375],
  [-1.990369453, 83.539784281],
  [-1.961570561, 83.733930644],
  [-1.913880671, 83.924319355],
  [-1.847759065, 84.109116865],
  [-1.763842529, 84.286543474],
  [-1.662939225, 84.454890466],
  [-1.546020907, 84.612536568],
  [-1.414213562, 84.757963562],
  [-1.268786568, 84.889770907],
  [-1.111140466, 85.006689225],
  [-0.942793474, 85.107592529],
  [-0.765366865, 85.191509065],
  [-0.580569355, 85.257630671],
  [-0.390180644, 85.305320561],
  [-0.196034281, 85.334119453],
  [0.0, 85.34375],
  [17.05, 85.34375],
  [17.05, 100.39375],
  [0.0, 100.39375],
  [-0.196034281, 100.403380547],
  [-0.390180644, 100.432179439],
  [-0.580569355, 100.479869329],
  [-0.765366865, 100.545990935],
  [-0.942793474, 100.629907471],
  [-1.111140466, 100.730810775],
  [-1.268786568, 100.847729093],
  [-1.414213562, 100.979536438],
  [-1.546020907, 101.124963432],
  [-1.662939225, 101.282609534],
  [-1.763842529, 101.450956526],
  [-1.847759065, 101.628383135],
  [-1.913880671, 101.813180645],
  [-1.961570561, 102.003569356],
  [-1.990369453, 102.197715719],
  [-2.0, 102.39375],
  [-2.0, 121.44375],
  [-1.990369453, 121.639784281],
  [-1.961570561, 121.833930644],
  [-1.913880671, 122.024319355],
  [-1.847759065, 122.209116865],
  [-1.763842529, 122.386543474],
  [-1.662939225, 122.554890466],
  [-1.546020907, 122.712536568],
  [-1.414213562, 122.857963562],
  [-1.268786568, 122.989770907],
  [-1.111140466, 123.106689225],
  [-0.942793474, 123.207592529],
  [-0.765366865, 123.291509065],
  [-0.580569355, 123.357630671],
  [-0.390180644, 123.405320561],
  [-0.196034281, 123.434119453],
  [0.0, 123.44375],
  [57.15, 123.44375],
  [57.346034281, 123.434119453],
  [57.540180644, 123.405320561],
  [57.730569355, 123.357630671],
  [57.915366865, 123.291509065],
  [58.092793474, 123.207592529],
  [58.261140466, 123.106689225],
  [58.418786568, 122.989770907],
  [58.564213562, 122.857963562],
  [58.696020907, 122.712536568],
  [58.812939225, 122.554890466],
  [58.913842529, 122.386543474],
  [58.997759065, 122.209116865],
  [59.063880671, 122.024319355],
  [59.111570561, 121.833930644],
  [59.140369453, 121.639784281],
  [59.15, 121.44375],
  [59.15, 102.39375],
  [59.140369453, 102.197715719],
  [59.111570561, 102.003569356],
  [59.063880671, 101.813180645],
  [58.997759065, 101.628383135],
  [58.913842529, 101.450956526],
  [58.812939225, 101.282609534],
  [58.696020907, 101.124963432],
  [58.564213562, 100.979536438],
  [58.418786568, 100.847729093],
  [58.261140466, 100.730810775],
  [58.092793474, 100.629907471],
  [57.915366865, 100.545990935],
  [57.730569355, 100.479869329],
  [57.540180644, 100.432179439],
  [57.346034281, 100.403380547],
  [57.15, 100.39375],
  [40.1, 100.39375],
  [40.1, 80.58125],
  [57.15, 80.58125],
  [57.346034281, 80.571619453],
  [57.540180644, 80.542820561],
  [57.730569355, 80.495130671],
  [57.915366865, 80.429009065],
  [58.092793474, 80.345092529],
  [58.261140466, 80.244189225],
  [58.418786568, 80.127270907],
  [58.564213562, 79.995463562],
  [58.696020907, 79.850036568],
  [58.812939225, 79.692390466],
  [58.913842529, 79.524043474],
  [58.997759065, 79.346616865],
  [59.063880671, 79.161819355],
  [59.111570561, 78.971430644],
  [59.140369453, 78.777284281],
  [59.15, 78.58125],
  [59.15, 78.2],
  [74.2, 78.2],
  [74.2, 78.58125],
  [74.209630547, 78.777284281],
  [74.238429439, 78.971430644],
  [74.286119329, 79.161819355],
  [74.352240935, 79.346616865],
  [74.436157471, 79.524043474],
  [74.537060775, 79.692390466],
  [74.653979093, 79.850036568],
  [74.785786438, 79.995463562],
  [74.931213432, 80.127270907],
  [75.088859534, 80.244189225],
  [75.257206526, 80.345092529],
  [75.434633135, 80.429009065],
  [75.619430645, 80.495130671],
  [75.809819356, 80.542820561],
  [76.003965719, 80.571619453],
  [76.2, 80.58125],
  [93.25, 80.58125],
  [93.25, 80.9625],
  [93.259630547, 81.158534281],
  [93.288429439, 81.352680644],
  [93.336119329, 81.543069355],
  [93.402240935, 81.727866865],
  [93.486157471, 81.905293474],
  [93.587060775, 82.073640466],
  [93.703979093, 82.231286568],
  [93.835786438, 82.376713562],
  [93.981213432, 82.508520907],
  [94.138859534, 82.625439225],
  [94.307206526, 82.726342529],
  [94.484633135, 82.810259065],
  [94.669430645, 82.876380671],
  [94.859819356, 82.924070561],
  [95.053965719, 82.952869453],
  [95.25, 82.9625],
  [106.34459234343457, 82.9625],
  [103.048195938, 101.657293001],
  [99.740198154, 120.417880696],
  [99.715641395, 120.612609102],
  [99.710289606, 120.808806821],
  [99.724194326, 121.004584362],
  [99.757221646, 121.198056279],
  [99.809053494, 121.387359333],
  [99.879190702, 121.570670431],
  [99.966957809, 121.746224187],
  [100.071509571, 121.912329924],
  [100.191839098, 122.067387951],
  [100.326787548, 122.209904975],
  [100.475055297, 122.33850848],
  [100.635214443, 122.451959943],
  [100.805722568, 122.549166764],
  [100.984937583, 122.62919279],
  [101.171133552, 122.691267324],
  [101.362517305, 122.734792557],
  [120.123105, 126.042790342],
  [138.883692694, 129.350788126],
  [139.0784211, 129.375344885],
  [139.274618819, 129.380696674],
  [139.47039636, 129.366791954],
  [139.663868277, 129.333764634],
  [139.853171331, 129.281932786],
  [140.036482429, 129.211795578],
  [140.212036185, 129.124028471],
  [140.378141922, 129.019476709],
  [140.533199949, 128.899147183],
  [140.675716973, 128.764198732],
  [140.804320478, 128.615930983],
  [140.917771941, 128.455771837],
  [141.014978762, 128.285263712],
  [141.095004788, 128.106048697],
  [141.157079322, 127.919852728],
  [141.200604555, 127.728468975],
  [144.50860234, 108.967881281],
  [147.816600125, 90.207293586],
  [151.124597909, 71.446705891],
  [151.149154668, 71.251977485],
  [151.154506457, 71.055779766],
  [151.140601737, 70.860002225],
  [151.107574417, 70.666530308],
  [151.055742569, 70.477227254],
  [150.985605361, 70.293916156],
  [150.897838254, 70.1183624],
  [150.793286492, 69.952256663],
  [150.672956965, 69.797198636],
  [150.538008515, 69.654681612],
  [150.389740766, 69.526078107],
  [150.22958162, 69.412626644],
  [150.059073495, 69.315419823],
  [149.87985848, 69.235393797],
  [149.693662511, 69.173319263],
  [149.502278758, 69.12979403],
  [133.40339680948836, 66.29112678287285],
  [133.546034281, 66.284119453],
  [133.740180644, 66.255320561],
  [133.930569355, 66.207630671],
  [134.115366865, 66.141509065],
  [134.292793474, 66.057592529],
  [134.461140466, 65.956689225],
  [134.618786568, 65.839770907],
  [134.764213562, 65.707963562],
  [134.896020907, 65.562536568],
  [135.012939225, 65.404890466],
  [135.113842529, 65.236543474],
  [135.197759065, 65.059116865],
  [135.263880671, 64.874319355],
  [135.311570561, 64.683930644],
  [135.340369453, 64.489784281],
  [135.35, 64.29375],
  [135.35, 7.14375],
  [135.340369453, 6.947715719],
  [135.311570561, 6.753569356],
  [135.263880671, 6.563180645],
  [135.197759065, 6.378383135],
  [135.113842529, 6.200956526],
  [135.012939225, 6.032609534],
  [134.896020907, 5.874963432],
  [134.764213562, 5.729536438],
  [134.618786568, 5.597729093],
  [134.461140466, 5.480810775],
  [134.292793474, 5.379907471],
  [134.115366865, 5.295990935],
  [133.930569355, 5.229869329],
  [133.740180644, 5.182179439],
  [133.546034281, 5.153380547],
  [133.35, 5.14375],
  [116.3, 5.14375],
  [116.3, 4.7625],
  [116.290369453, 4.566465719],
  [116.261570561, 4.372319356],
  [116.213880671, 4.181930645],
  [116.147759065, 3.997133135],
  [116.063842529, 3.819706526],
  [115.962939225, 3.651359534],
  [115.846020907, 3.493713432],
  [115.714213562, 3.348286438],
  [115.568786568, 3.216479093],
  [115.411140466, 3.099560775],
  [115.242793474, 2.998657471],
  [115.065366865, 2.914740935],
  [114.880569355, 2.848619329],
  [114.690180644, 2.800929439],
  [114.496034281, 2.772130547],
  [114.3, 2.7625],
  [97.25, 2.7625],
  [97.25, 2.38125],
  [97.240369453, 2.185215719],
  [97.211570561, 1.991069356],
  [97.163880671, 1.800680645],
  [97.097759065, 1.615883135],
  [97.013842529, 1.438456526],
  [96.912939225, 1.270109534],
  [96.796020907, 1.112463432],
  [96.664213562, 0.967036438],
  [96.518786568, 0.835229093],
  [96.361140466, 0.718310775],
  [96.192793474, 0.617407471],
  [96.015366865, 0.533490935],
  [95.830569355, 0.467369329],
  [95.640180644, 0.419679439],
  [95.446034281, 0.390880547],
  [95.25, 0.38125],
  [78.2, 0.38125],
  [78.2, 0.0],
  [78.190369453, -0.196034281],
  [78.161570561, -0.390180644],
  [78.113880671, -0.580569355],
  [78.047759065, -0.765366865],
  [77.963842529, -0.942793474],
  [77.862939225, -1.111140466],
  [77.746020907, -1.268786568],
  [77.614213562, -1.414213562],
  [77.468786568, -1.546020907],
  [77.311140466, -1.662939225],
  [77.142793474, -1.763842529],
  [76.965366865, -1.847759065],
  [76.780569355, -1.913880671],
  [76.590180644, -1.961570561],
  [76.396034281, -1.990369453],
  [76.2, -2.0],
  [57.15, -2.0],
  [56.953965719, -1.990369453],
  [56.759819356, -1.961570561],
  [56.569430645, -1.913880671],
  [56.384633135, -1.847759065],
  [56.207206526, -1.763842529],
  [56.038859534, -1.662939225],
  [55.881213432, -1.546020907],
  [55.735786438, -1.414213562],
  [55.603979093, -1.268786568],
  [55.487060775, -1.111140466],
  [55.386157471, -0.942793474],
  [55.302240935, -0.765366865],
  [55.236119329, -0.580569355],
  [55.188429439, -0.390180644],
  [55.159630547, -0.196034281],
  [55.15, 0.0],
  [55.15, 0.38125],
  [38.1, 0.38125],
  [37.903965719, 0.390880547],
  [37.709819356, 0.419679439],
  [37.519430645, 0.467369329],
  [37.334633135, 0.533490935],
  [37.157206526, 0.617407471],
  [36.988859534, 0.718310775],
  [36.831213432, 0.835229093],
  [36.685786438, 0.967036438],
  [36.553979093, 1.112463432],
  [36.437060775, 1.270109534],
  [36.336157471, 1.438456526],
  [36.252240935, 1.615883135],
  [36.186119329, 1.800680645],
  [36.138429439, 1.991069356],
  [36.109630547, 2.185215719],
  [36.1, 2.38125],
  [36.1, 5.14375],
  [0.0, 5.14375],
  [-0.196034281, 5.153380547],
  [-0.390180644, 5.182179439],
  [-0.580569355, 5.229869329],
  [-0.765366865, 5.295990935],
  [-0.942793474, 5.379907471],
  [-1.111140466, 5.480810775],
  [-1.268786568, 5.597729093],
  [-1.414213562, 5.729536438],
  [-1.546020907, 5.874963432],
  [-1.662939225, 6.032609534],
  [-1.763842529, 6.200956526],
  [-1.847759065, 6.378383135],
  [-1.913880671, 6.563180645],
  [-1.961570561, 6.753569356],
  [-1.990369453, 6.947715719],
  [-2.0, 7.14375],
  [-2.0, 83.34375],
  [104.525407567, 101.917765267],
  [107.833405352, 83.157177573],
  [107.844286661, 83.109331635],
  [107.859805294, 83.062782643],
  [107.879811801, 83.017978889],
  [107.904113506, 82.975351858],
  [107.932476372, 82.935312071],
  [107.964627248, 82.898245134],
  [108.000256504, 82.864508021],
  [108.039021011, 82.83442564],
  [108.080547445, 82.808287699],
  [108.124435884, 82.786345922],
  [108.170263659, 82.768811621],
  [108.217589422, 82.755853658],
  [108.265957401, 82.747596828],
  [108.314901786, 82.744120648],
  [108.363951216, 82.745458596],
  [108.412633318, 82.751597785],
  [126.680817136, 85.972771481],
  [129.901990831, 67.704587662],
  [129.91287214, 67.656741724],
  [129.928390773, 67.610192732],
  [129.94839728, 67.565388978],
  [129.972698985, 67.522761947],
  [130.001061851, 67.48272216],
  [130.033212727, 67.445655223],
  [130.068841983, 67.41191811],
  [130.10760649, 67.381835729],
  [130.149132924, 67.355697788],
  [130.193021363, 67.333756011],
  [130.238849138, 67.31622171],
  [130.286174901, 67.303263747],
  [130.33454288, 67.295006917],
  [130.383487265, 67.291530737],
  [130.432536695, 67.292868685],
  [130.481218797, 67.299007874],
  [149.241806492, 70.607005659],
  [149.28965243, 70.617886968],
  [149.336201422, 70.633405601],
  [149.381005176, 70.653412108],
  [149.423632207, 70.677713813],
  [149.463671994, 70.706076679],
  [149.500738931, 70.738227555],
  [149.534476044, 70.773856811],
  [149.564558425, 70.812621318],
  [149.590696366, 70.854147752],
  [149.612638143, 70.898036191],
  [149.630172444, 70.943863966],
  [149.643130407, 70.991189729],
  [149.651387237, 71.039557708],
  [149.654863417, 71.088502093],
  [149.653525469, 71.137551523],
  [149.64738628, 71.186233625],
  [146.339388496, 89.94682132],
  [143.031390711, 108.707409015],
  [139.723392926, 127.467996709],
  [139.712511617, 127.515842647],
  [139.696992984, 127.562391639],
  [139.676986477, 127.607195393],
  [139.652684772, 127.649822424],
  [139.624321906, 127.689862211],
  [139.59217103, 127.726929148],
  [139.556541774, 127.760666261],
  [139.517777267, 127.790748642],
  [139.476250833, 127.816886583],
  [139.432362394, 127.83882836],
  [139.386534619, 127.856362661],
  [139.339208856, 127.869320624],
  [139.290840877, 127.877577454],
  [139.241896492, 127.881053634],
  [139.192847062, 127.879715686],
  [139.14416496, 127.873576497],
  [120.383577266, 124.565578713],
  [101.622989571, 121.257580928],
  [101.575143633, 121.246699619],
  [101.528594641, 121.231180986],
  [101.483790887, 121.211174479],
  [101.441163856, 121.186872774],
  [101.401124069, 121.158509908],
  [101.364057132, 121.126359032],
  [101.330320019, 121.090729776],
  [101.300237638, 121.051965269],
  [101.274099697, 121.010438835],
  [101.25215792, 120.966550396],
  [101.234623619, 120.920722621],
  [101.221665656, 120.873396858],
  [101.213408826, 120.825028879],
  [101.209932646, 120.776084494],
  [101.211270594, 120.727035064],
  [101.217409783, 120.678352962],
  [104.525407567, 101.917765267],
  [-0.5, 83.34375],
  [-0.5, 7.14375],
  [-0.497592363, 7.09474143],
  [-0.49039264, 7.046204839],
  [-0.478470168, 6.998607661],
  [-0.461939766, 6.952408284],
  [-0.440960632, 6.908051632],
  [-0.415734806, 6.865964883],
  [-0.386505227, 6.826553358],
  [-0.353553391, 6.790196609],
  [-0.317196642, 6.757244773],
  [-0.277785117, 6.728015194],
  [-0.235698368, 6.702789368],
  [-0.191341716, 6.681810234],
  [-0.145142339, 6.665279832],
  [-0.097545161, 6.65335736],
  [-0.04900857, 6.646157637],
  [0.0, 6.64375],
  [37.6, 6.64375],
  [37.6, 2.38125],
  [37.602407637, 2.33224143],
  [37.60960736, 2.283704839],
  [37.621529832, 2.236107661],
  [37.638060234, 2.189908284],
  [37.659039368, 2.145551632],
  [37.684265194, 2.103464883],
  [37.713494773, 2.064053358],
  [37.746446609, 2.027696609],
  [37.782803358, 1.994744773],
  [37.822214883, 1.965515194],
  [37.864301632, 1.940289368],
  [37.908658284, 1.919310234],
  [37.954857661, 1.902779832],
  [38.002454839, 1.89085736],
  [38.05099143, 1.883657637],
  [38.1, 1.88125],
  [56.65, 1.88125],
  [56.65, 0.0],
  [56.652407637, -0.04900857],
  [56.65960736, -0.097545161],
  [56.671529832, -0.145142339],
  [56.688060234, -0.191341716],
  [56.709039368, -0.235698368],
  [56.734265194, -0.277785117],
  [56.763494773, -0.317196642],
  [56.796446609, -0.353553391],
  [56.832803358, -0.386505227],
  [56.872214883, -0.415734806],
  [56.914301632, -0.440960632],
  [56.958658284, -0.461939766],
  [57.004857661, -0.478470168],
  [57.052454839, -0.49039264],
  [57.10099143, -0.497592363],
  [57.15, -0.5],
  [76.2, -0.5],
  [76.24900857, -0.497592363],
  [76.297545161, -0.49039264],
  [76.345142339, -0.478470168],
  [76.391341716, -0.461939766],
  [76.435698368, -0.440960632],
  [76.477785117, -0.415734806],
  [76.517196642, -0.386505227],
  [76.553553391, -0.353553391],
  [76.586505227, -0.317196642],
  [76.615734806, -0.277785117],
  [76.640960632, -0.235698368],
  [76.661939766, -0.191341716],
  [76.678470168, -0.145142339],
  [76.69039264, -0.097545161],
  [76.697592363, -0.04900857],
  [76.7, 0.0],
  [76.7, 1.88125],
  [95.25, 1.88125],
  [95.29900857, 1.883657637],
  [95.347545161, 1.89085736],
  [95.395142339, 1.902779832],
  [95.441341716, 1.919310234],
  [95.485698368, 1.940289368],
  [95.527785117, 1.965515194],
  [95.567196642, 1.994744773],
  [95.603553391, 2.027696609],
  [95.636505227, 2.064053358],
  [95.665734806, 2.103464883],
  [95.690960632, 2.145551632],
  [95.711939766, 2.189908284],
  [95.728470168, 2.236107661],
  [95.74039264, 2.283704839],
  [95.747592363, 2.33224143],
  [95.75, 2.38125],
  [95.75, 4.2625],
  [114.3, 4.2625],
  [114.34900857, 4.264907637],
  [114.397545161, 4.27210736],
  [114.445142339, 4.284029832],
  [114.491341716, 4.300560234],
  [114.535698368, 4.321539368],
  [114.577785117, 4.346765194],
  [114.617196642, 4.375994773],
  [114.653553391, 4.408946609],
  [114.686505227, 4.445303358],
  [114.715734806, 4.484714883],
  [114.740960632, 4.526801632],
  [114.761939766, 4.571158284],
  [114.778470168, 4.617357661],
  [114.79039264, 4.664954839],
  [114.797592363, 4.71349143],
  [114.8, 4.7625],
  [114.8, 6.64375],
  [133.35, 6.64375],
  [133.39900857, 6.646157637],
  [133.447545161, 6.65335736],
  [133.495142339, 6.665279832],
  [133.541341716, 6.681810234],
  [133.585698368, 6.702789368],
  [133.627785117, 6.728015194],
  [133.667196642, 6.757244773],
  [133.703553391, 6.790196609],
  [133.736505227, 6.826553358],
  [133.765734806, 6.865964883],
  [133.790960632, 6.908051632],
  [133.811939766, 6.952408284],
  [133.828470168, 6.998607661],
  [133.84039264, 7.046204839],
  [133.847592363, 7.09474143],
  [133.85, 7.14375],
  [133.85, 64.29375],
  [133.847592363, 64.34275857],
  [133.84039264, 64.391295161],
  [133.828470168, 64.438892339],
  [133.811939766, 64.485091716],
  [133.790960632, 64.529448368],
  [133.765734806, 64.571535117],
  [133.736505227, 64.610946642],
  [133.703553391, 64.647303391],
  [133.667196642, 64.680255227],
  [133.627785117, 64.709484806],
  [133.585698368, 64.734710632],
  [133.541341716, 64.755689766],
  [133.495142339, 64.772220168],
  [133.447545161, 64.78414264],
  [133.39900857, 64.791342363],
  [133.35, 64.79375],
  [114.8, 64.79375],
  [114.8, 80.9625],
  [114.797592363, 81.01150857],
  [114.79039264, 81.060045161],
  [114.778470168, 81.107642339],
  [114.761939766, 81.153841716],
  [114.740960632, 81.198198368],
  [114.715734806, 81.240285117],
  [114.686505227, 81.279696642],
  [114.653553391, 81.316053391],
  [114.617196642, 81.349005227],
  [114.577785117, 81.378234806],
  [114.535698368, 81.403460632],
  [114.491341716, 81.424439766],
  [114.445142339, 81.440970168],
  [114.397545161, 81.45289264],
  [114.34900857, 81.460092363],
  [114.3, 81.4625],
  [95.25, 81.4625],
  [95.20099143, 81.460092363],
  [95.152454839, 81.45289264],
  [95.104857661, 81.440970168],
  [95.058658284, 81.424439766],
  [95.014301632, 81.403460632],
  [94.972214883, 81.378234806],
  [94.932803358, 81.349005227],
  [94.896446609, 81.316053391],
  [94.863494773, 81.279696642],
  [94.834265194, 81.240285117],
  [94.809039368, 81.198198368],
  [94.788060234, 81.153841716],
  [94.771529832, 81.107642339],
  [94.75960736, 81.060045161],
  [94.752407637, 81.01150857],
  [94.75, 80.9625],
  [94.75, 79.08125],
  [76.2, 79.08125],
  [76.15099143, 79.078842363],
  [76.102454839, 79.07164264],
  [76.054857661, 79.059720168],
  [76.008658284, 79.043189766],
  [75.964301632, 79.022210632],
  [75.922214883, 78.996984806],
  [75.882803358, 78.967755227],
  [75.846446609, 78.934803391],
  [75.813494773, 78.898446642],
  [75.784265194, 78.859035117],
  [75.759039368, 78.816948368],
  [75.738060234, 78.772591716],
  [75.721529832, 78.726392339],
  [75.70960736, 78.678795161],
  [75.702407637, 78.63025857],
  [75.7, 78.58125],
  [75.7, 76.7],
  [57.65, 76.7],
  [57.65, 78.58125],
  [57.647592363, 78.63025857],
  [57.64039264, 78.678795161],
  [57.628470168, 78.726392339],
  [57.611939766, 78.772591716],
  [57.590960632, 78.816948368],
  [57.565734806, 78.859035117],
  [57.536505227, 78.898446642],
  [57.503553391, 78.934803391],
  [57.467196642, 78.967755227],
  [57.427785117, 78.996984806],
  [57.385698368, 79.022210632],
  [57.341341716, 79.043189766],
  [57.295142339, 79.059720168],
  [57.247545161, 79.07164264],
  [57.19900857, 79.078842363],
  [57.15, 79.08125],
  [38.6, 79.08125],
  [38.6, 101.89375],
  [57.15, 101.89375],
  [57.19900857, 101.896157637],
  [57.247545161, 101.90335736],
  [57.295142339, 101.915279832],
  [57.341341716, 101.931810234],
  [57.385698368, 101.952789368],
  [57.427785117, 101.978015194],
  [57.467196642, 102.007244773],
  [57.503553391, 102.040196609],
  [57.536505227, 102.076553358],
  [57.565734806, 102.115964883],
  [57.590960632, 102.158051632],
  [57.611939766, 102.202408284],
  [57.628470168, 102.248607661],
  [57.64039264, 102.296204839],
  [57.647592363, 102.34474143],
  [57.65, 102.39375],
  [57.65, 121.44375],
  [57.647592363, 121.49275857],
  [57.64039264, 121.541295161],
  [57.628470168, 121.588892339],
  [57.611939766, 121.635091716],
  [57.590960632, 121.679448368],
  [57.565734806, 121.721535117],
  [57.536505227, 121.760946642],
  [57.503553391, 121.797303391],
  [57.467196642, 121.830255227],
  [57.427785117, 121.859484806],
  [57.385698368, 121.884710632],
  [57.341341716, 121.905689766],
  [57.295142339, 121.922220168],
  [57.247545161, 121.93414264],
  [57.19900857, 121.941342363],
  [57.15, 121.94375],
  [0.0, 121.94375],
  [-0.04900857, 121.941342363],
  [-0.097545161, 121.93414264],
  [-0.145142339, 121.922220168],
  [-0.191341716, 121.905689766],
  [-0.235698368, 121.884710632],
  [-0.277785117, 121.859484806],
  [-0.317196642, 121.830255227],
  [-0.353553391, 121.797303391],
  [-0.386505227, 121.760946642],
  [-0.415734806, 121.721535117],
  [-0.440960632, 121.679448368],
  [-0.461939766, 121.635091716],
  [-0.478470168, 121.588892339],
  [-0.49039264, 121.541295161],
  [-0.497592363, 121.49275857],
  [-0.5, 121.44375],
  [-0.5, 102.39375],
  [-0.497592363, 102.34474143],
  [-0.49039264, 102.296204839],
  [-0.478470168, 102.248607661],
  [-0.461939766, 102.202408284],
  [-0.440960632, 102.158051632],
  [-0.415734806, 102.115964883],
  [-0.386505227, 102.076553358],
  [-0.353553391, 102.040196609],
  [-0.317196642, 102.007244773],
  [-0.277785117, 101.978015194],
  [-0.235698368, 101.952789368],
  [-0.191341716, 101.931810234],
  [-0.145142339, 101.915279832],
  [-0.097545161, 101.90335736],
  [-0.04900857, 101.896157637],
  [0.0, 101.89375],
  [18.55, 101.89375],
  [18.55, 83.84375],
  [0.0, 83.84375],
  [-0.04900857, 83.841342363],
  [-0.097545161, 83.83414264],
  [-0.145142339, 83.822220168],
  [-0.191341716, 83.805689766],
  [-0.235698368, 83.784710632],
  [-0.277785117, 83.759484806],
  [-0.317196642, 83.730255227],
  [-0.353553391, 83.697303391],
  [-0.386505227, 83.660946642],
  [-0.415734806, 83.621535117],
  [-0.440960632, 83.579448368],
  [-0.461939766, 83.535091716],
  [-0.478470168, 83.488892339],
  [-0.49039264, 83.441295161],
  [-0.497592363, 83.39275857],
  [-0.5, 83.34375],
  [129.07073175447294, 66.29375],
  [128.949666784, 66.408385639],
  [128.821063279, 66.556653388],
  [128.707611816, 66.716812534],
  [128.610404995, 66.887320659],
  [128.530378969, 67.066535674],
  [128.468304435, 67.252731643],
  [128.424779202, 67.444115396],
  [125.464077773, 84.235087585],
  [115.58563387444819, 82.49325139841524],
  [115.714213562, 82.376713562],
  [115.846020907, 82.231286568],
  [115.962939225, 82.073640466],
  [116.063842529, 81.905293474],
  [116.147759065, 81.727866865],
  [116.213880671, 81.543069355],
  [116.261570561, 81.352680644],
  [116.290369453, 81.158534281],
  [116.3, 80.9625],
  [116.3, 66.29375],
  [129.07073175447294, 66.29375]
  ], [
  [
  0,
  1,
  2,
  3,
  4,
  5,
  6,
  7,
  8,
  9,
  10,
  11,
  12,
  13,
  14,
  15,
  16,
  17,
  18,
  19,
  20,
  21,
  22,
  23,
  24,
  25,
  26,
  27,
  28,
  29,
  30,
  31,
  32,
  33,
  34,
  35,
  36,
  37,
  38,
  39,
  40,
  41,
  42,
  43,
  44,
  45,
  46,
  47,
  48,
  49,
  50,
  51,
  52,
  53,
  54,
  55,
  56,
  57,
  58,
  59,
  60,
  61,
  62,
  63,
  64,
  65,
  66,
  67,
  68,
  69,
  70,
  71,
  72,
  73,
  74,
  75,
  76,
  77,
  78,
  79,
  80,
  81,
  82,
  83,
  84,
  85,
  86,
  87,
  88,
  89,
  90,
  91,
  92,
  93,
  94,
  95,
  96,
  97,
  98,
  99,
  100,
  101,
  102,
  103,
  104,
  105,
  106,
  107,
  108,
  109,
  110,
  111,
  112,
  113,
  114,
  115,
  116,
  117,
  118,
  119,
  120,
  121,
  122,
  123,
  124,
  125,
  126,
  127,
  128,
  129,
  130,
  131,
  132,
  133,
  134,
  135,
  136,
  137,
  138,
  139,
  140,
  141,
  142,
  143,
  144,
  145,
  146,
  147,
  148,
  149,
  150,
  151,
  152,
  153,
  154,
  155,
  156,
  157,
  158,
  159,
  160,
  161,
  162,
  163,
  164,
  165,
  166,
  167,
  168,
  169,
  170,
  171,
  172,
  173,
  174,
  175,
  176,
  177,
  178,
  179,
  180,
  181,
  182,
  183,
  184,
  185,
  186,
  187,
  188,
  189,
  190,
  191,
  192,
  193,
  194,
  195,
  196,
  197,
  198,
  199,
  200,
  201,
  202,
  203,
  204,
  205,
  206,
  207,
  208,
  209,
  210,
  211,
  212,
  213,
  214,
  215,
  216,
  217,
  218,
  219,
  220,
  221,
  222,
  223,
  224,
  225,
  226,
  227,
  228,
  229,
  230,
  231,
  232,
  233,
  234,
  235,
  236,
  237,
  238,
  239,
  240,
  241,
  242,
  243,
  244,
  245,
  246,
  247,
  248,
  249,
  250,
  251,
  252,
  253,
  254,
  255,
  256,
  257,
  258,
  259,
  260,
  261,
  262,
  263,
  264,
  265,
  266,
  267,
  268,
  269,
  270,
  271,
  272,
  273,
  274,
  275,
  276,
  277,
  278,
  279,
  280,
  281,
  282,
  283,
  284,
  285,
  286,
  287,
  288,
  289,
  290,
  291,
  292,
  293,
  294,
  295,
  296,
  297,
  298,
  299,
  300,
  301,
  302,
  303,
  304,
  305,
  306,
  307,
  308,
  309,
  310,
  311,
  312,
  313,
  314,
  315,
  316,
  317,
  318,
  319,
  320,
  321,
  322,
  323,
  324,
  325,
  326,
  327,
  328,
  329,
  330,
  331,
  332,
  333,
  334,
  335,
  336,
  337,
  338,
  339,
  340
  ],
  [
  341,
  342,
  343,
  344,
  345,
  346,
  347,
  348,
  349,
  350,
  351,
  352,
  353,
  354,
  355,
  356,
  357,
  358,
  359,
  360,
  361,
  362,
  363,
  364,
  365,
  366,
  367,
  368,
  369,
  370,
  371,
  372,
  373,
  374,
  375,
  376,
  377,
  378,
  379,
  380,
  381,
  382,
  383,
  384,
  385,
  386,
  387,
  388,
  389,
  390,
  391,
  392,
  393,
  394,
  395,
  396,
  397,
  398,
  399,
  400,
  401,
  402,
  403,
  404,
  405,
  406,
  407,
  408,
  409,
  410,
  411,
  412,
  413,
  414,
  415,
  416,
  417,
  418,
  419,
  420,
  421,
  422,
  423,
  424,
  425,
  426,
  427,
  428,
  429,
  430,
  431
  ],
  [
  432,
  433,
  434,
  435,
  436,
  437,
  438,
  439,
  440,
  441,
  442,
  443,
  444,
  445,
  446,
  447,
  448,
  449,
  450,
  451,
  452,
  453,
  454,
  455,
  456,
  457,
  458,
  459,
  460,
  461,
  462,
  463,
  464,
  465,
  466,
  467,
  468,
  469,
  470,
  471,
  472,
  473,
  474,
  475,
  476,
  477,
  478,
  479,
  480,
  481,
  482,
  483,
  484,
  485,
  486,
  487,
  488,
  489,
  490,
  491,
  492,
  493,
  494,
  495,
  496,
  497,
  498,
  499,
  500,
  501,
  502,
  503,
  504,
  505,
  506,
  507,
  508,
  509,
  510,
  511,
  512,
  513,
  514,
  515,
  516,
  517,
  518,
  519,
  520,
  521,
  522,
  523,
  524,
  525,
  526,
  527,
  528,
  529,
  530,
  531,
  532,
  533,
  534,
  535,
  536,
  537,
  538,
  539,
  540,
  541,
  542,
  543,
  544,
  545,
  546,
  547,
  548,
  549,
  550,
  551,
  552,
  553,
  554,
  555,
  556,
  557,
  558,
  559,
  560,
  561,
  562,
  563,
  564,
  565,
  566,
  567,
  568,
  569,
  570,
  571,
  572,
  573,
  574,
  575,
  576,
  577,
  578,
  579,
  580,
  581,
  582,
  583,
  584,
  585,
  586,
  587,
  588,
  589,
  590,
  591,
  592,
  593,
  594,
  595,
  596,
  597,
  598,
  599,
  600,
  601,
  602,
  603,
  604,
  605,
  606,
  607,
  608,
  609,
  610,
  611,
  612,
  613,
  614,
  615,
  616,
  617,
  618,
  619,
  620,
  621,
  622,
  623,
  624,
  625,
  626,
  627,
  628,
  629,
  630,
  631,
  632,
  633,
  634,
  635,
  636,
  637,
  638,
  639,
  640,
  641,
  642,
  643,
  644,
  645,
  646,
  647,
  648,
  649,
  650,
  651,
  652,
  653,
  654,
  655,
  656,
  657,
  658,
  659,
  660,
  661,
  662,
  663,
  664,
  665,
  666,
  667,
  668,
  669,
  670,
  671,
  672,
  673,
  674,
  675,
  676,
  677,
  678,
  679,
  680,
  681,
  682,
  683,
  684,
  685,
  686,
  687,
  688,
  689,
  690,
  691,
  692,
  693,
  694,
  695,
  696,
  697,
  698,
  699,
  700,
  701,
  702,
  703,
  704,
  705,
  706,
  707,
  708,
  709,
  710,
  711,
  712,
  713,
  714,
  715,
  716,
  717,
  718,
  719,
  720,
  721,
  722,
  723,
  724,
  725,
  726,
  727,
  728,
  729,
  730,
  731,
  732,
  733,
  734
  ],
  [
  735,
  736,
  737,
  738,
  739,
  740,
  741,
  742,
  743,
  744,
  745,
  746,
  747,
  748,
  749,
  750,
  751,
  752,
  753,
  754,
  755
  ]
  ]);
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
