wez/halfdeck/case/switch-plate.scad

mirror([0, 1, 0]) color("grey") {
union() {
linear_extrude(height=2) {
polygon([[119.9620436791635, -10.0], [119.88614853201763, -9.998847719777999], [53.880686985647216, -7.994126032720432], [53.646495296320076, -7.975973004726603], [-5.810086836473021, -0.5439002381274649], [-6.047487665291121, -0.5025204617148387], [-6.279801550623147, -0.4384759607689326], [-6.504869964194179, -0.3523618003068363], [-6.720601698525187, -0.2449781040489396], [-6.9249922972416, -0.11732262012514494], [-7.116142679340018, 0.029418549432351115], [-7.292276784366992, 0.19388196927341883], [-7.451758074560958, 0.3745395389945354], [-7.593104740628792, 0.569712691377185], [-7.71500346987358, 0.7775879886781831], [-7.816321648748018, 0.9962339720600868], [-7.896117886454252, 1.2236191076063734], [-7.953650761810862, 1.45763066217724], [-7.988385712116106, 1.69609433372233], [-8.0, 1.9367944536567043], [-8.000000000000002, 99.39375], [-7.999999999999999, 126.83538329329558], [-7.988630737664156, 127.07353671349598], [-7.954626358757477, 127.30952403072804], [-7.898296147043448, 127.54119884361772], [-7.820152448885596, 127.76645397478553], [-7.720906013247321, 127.98324063648849], [-7.601459527138758, 128.18958706518433], [-7.462899405308439, 128.38361645552916], [-7.306485908855863, 128.56356403069117], [-7.133641682640258, 128.72779309371944], [-6.945938815742489, 128.87480991397337], [-6.745084542670518, 129.00327731321514], [-6.532905715361807, 129.11202682779387], [-6.311332187216184, 129.2000693363015], [-6.082379260288182, 129.26660405603724], [-5.848129355288844, 129.31102582645462], [-5.610713071115836, 129.33293061334462], [143.51094867944454, 135.94330272112006], [143.7578335033689, 135.94204409706296], [144.00339029973705, 135.9164401876724], [144.2452242532848, 135.86674069743202], [144.48097685611515, 135.79343032519606], [144.70834890926406, 135.69722403711918], [144.9251229458497, 135.57906009388333], [145.1291848571225, 135.44009090022388], [145.3185445105055, 135.2816717659965], [145.49135515854522, 135.10534768839287], [145.6459314494865, 134.91283828421348], [145.78076586382062, 134.70602101914633], [145.89454341650796, 134.48691289761004], [145.98615448149076, 134.25765079173254], [146.05470561342344, 134.02047060130883], [165.9330438628631, 49.86597310114771], [165.98320454827606, 49.58055907861434], [166.00000000000003, 49.291257900909926], [166.0, -6.398002531138397], [165.98859115294965, -6.63656923766047], [165.95446874123138, -6.872958527329727], [165.89794420274623, -7.105012856746026], [165.81953344134553, -7.3306142480280165], [165.7199521181364, -7.5477036197617124], [165.60010911958736, -7.754299580396419], [165.46109826205074, -7.9485165125592525], [165.30418830841614, -8.128581783231304], [165.13081138801294, -8.29285192270683], [164.9425499254547, -8.439827624668856], [164.7411221977268, -8.56816743047434], [164.52836665133918, -8.676699972751353], [164.3062251226821, -8.764434666560037], [164.07672511473476, -8.830570750538252], [163.8419612918881, -8.874504595512704], [163.60407636178044, -8.895835213869276], [137.156137109102, -9.99783268273088], [137.05206074732155, -10.0], [119.9620436791635, -10.0], [146.22988117819344, 73.14758746355804], [143.7988066908564, 86.93489600572894], [130.0114981486855, 84.50382151839193], [132.4425726360225, 70.71651297622101], [146.22988117819344, 73.14758746355804], [142.92188339363838, 91.90817515844061], [140.49080890630137, 105.69548370061152], [126.70350036413045, 103.2644092132745], [129.13457485146748, 89.4771006711036], [142.92188339363838, 91.90817515844061], [139.61388560908333, 110.66876285332319], [137.1828111217463, 124.45607139549409], [123.3955025795754, 122.02499690815708], [125.82657706691242, 108.23768836598617], [139.61388560908333, 110.66876285332319], [130.82500000000005, 47.768750000000004], [130.82500000000005, 61.768750000000004], [116.82500000000003, 61.768750000000004], [116.82500000000003, 47.768750000000004], [130.82500000000005, 47.768750000000004], [130.82500000000005, 28.718750000000007], [130.82500000000005, 42.71875000000001], [116.82500000000003, 42.71875000000001], [116.82500000000003, 28.718750000000007], [130.82500000000005, 28.718750000000007], [130.82500000000005, 9.668750000000003], [130.82500000000005, 23.668750000000003], [116.82500000000003, 23.668750000000003], [116.82500000000003, 9.668750000000003], [130.82500000000005, 9.668750000000003], [124.16129569875584, 88.60017737388559], [121.73022121141881, 102.3874859160565], [107.94291266924789, 99.95641142871948], [110.37398715658492, 86.16910288654856], [124.16129569875584, 88.60017737388559], [120.85329791420082, 107.36076506876817], [118.4222234268638, 121.14807361093908], [104.63491488469289, 118.71699912360204], [107.0659893720299, 104.92969058143115], [120.85329791420082, 107.36076506876817], [111.77500000000002, 7.287500000000003], [111.77500000000002, 21.2875], [97.77500000000002, 21.2875], [97.77500000000002, 7.287500000000003], [111.77500000000002, 7.287500000000003], [111.775, 64.4375], [111.775, 78.4375], [97.775, 78.4375], [97.775, 64.4375], [111.775, 64.4375], [111.775, 45.3875], [111.775, 59.3875], [97.775, 59.3875], [97.775, 45.3875], [111.775, 45.3875], [111.775, 26.3375], [111.775, 40.3375], [97.775, 40.3375], [97.775, 26.3375], [111.775, 26.3375], [92.725, 62.056250000000006], [92.725, 76.05625], [78.725, 76.05625], [78.725, 62.056250000000006], [92.725, 62.056250000000006], [92.725, 43.006249999999994], [92.725, 57.006249999999994], [78.725, 57.006249999999994], [78.725, 43.006249999999994], [92.725, 43.006249999999994], [92.725, 23.956250000000004], [92.725, 37.956250000000004], [78.725, 37.956250000000004], [78.725, 23.956250000000004], [92.725, 23.956250000000004], [92.725, 4.906250000000002], [92.725, 18.90625], [78.725, 18.90625], [78.725, 4.906250000000002], [92.725, 4.906250000000002], [73.67500000000001, 21.575], [73.67500000000001, 35.575], [59.67500000000001, 35.575], [59.67500000000001, 21.575], [73.67500000000001, 21.575], [73.67500000000001, 40.625], [73.67500000000001, 54.625], [59.67500000000001, 54.625], [59.67500000000001, 40.625], [73.67500000000001, 40.625], [73.67500000000001, 2.5249999999999986], [73.67500000000001, 16.525], [59.67500000000001, 16.525], [59.67500000000001, 2.5249999999999986], [73.67500000000001, 2.5249999999999986], [73.675, 59.675], [73.675, 73.675], [59.675, 73.675], [59.675, 59.675], [73.675, 59.675], [54.625, 104.91875], [54.625, 118.91875], [40.625, 118.91875], [40.625, 104.91875], [54.625, 104.91875], [54.625, 62.056250000000006], [54.625, 76.05625], [40.625, 76.05625], [40.625, 62.056250000000006], [54.625, 62.056250000000006], [54.625, 43.00625], [54.625, 57.00625], [40.625, 57.00625], [40.625, 43.00625], [54.625, 43.00625], [54.625, 23.95625], [54.625, 37.95625], [40.625, 37.95625], [40.625, 23.95625], [54.625, 23.95625], [54.625, 4.90625], [54.625, 18.90625], [40.625, 18.90625], [40.625, 4.90625], [54.625, 4.90625], [35.575, 85.86875], [35.575, 99.86875], [21.575, 99.86875], [21.575, 85.86875], [35.575, 85.86875], [35.575, 9.668750000000003], [35.575, 23.668750000000003], [21.575, 23.668750000000003], [21.575, 9.668750000000003], [35.575, 9.668750000000003], [35.575, 28.71875], [35.575, 42.71875], [21.575, 42.71875], [21.575, 28.71875], [35.575, 28.71875], [35.575, 47.768750000000004], [35.575, 61.768750000000004], [21.575, 61.768750000000004], [21.575, 47.768750000000004], [35.575, 47.768750000000004], [35.575, 66.81875], [35.575, 80.81875], [21.575, 80.81875], [21.575, 66.81875], [35.575, 66.81875], [35.575, 104.91875], [35.575, 118.91875], [21.575, 118.91875], [21.575, 104.91875], [35.575, 104.91875], [16.525, 9.668750000000003], [16.525, 23.668750000000003], [2.5250000000000004, 23.668750000000003], [2.5250000000000004, 9.668750000000003], [16.525, 9.668750000000003], [16.525, 104.91875], [16.525, 118.91875], [2.5249999999999986, 118.91875], [2.5249999999999986, 104.91875], [16.525, 104.91875], [16.525, 66.81875], [16.525, 80.81875], [2.5249999999999986, 80.81875], [2.5249999999999986, 66.81875], [16.525, 66.81875], [16.525, 47.768750000000004], [16.525, 61.768750000000004], [2.5250000000000004, 61.768750000000004], [2.5250000000000004, 47.768750000000004], [16.525, 47.768750000000004], [16.525, 28.71875], [16.525, 42.71875], [2.5250000000000004, 42.71875], [2.5250000000000004, 28.71875], [16.525, 28.71875]], [[0, 1, 2, 3, 4, 5, 6, 7, 8, 9, 10, 11, 12, 13, 14, 15, 16, 17, 18, 19, 20, 21, 22, 23, 24, 25, 26, 27, 28, 29, 30, 31, 32, 33, 34, 35, 36, 37, 38, 39, 40, 41, 42, 43, 44, 45, 46, 47, 48, 49, 50, 51, 52, 53, 54, 55, 56, 57, 58, 59, 60, 61, 62, 63, 64, 65, 66, 67, 68, 69, 70, 71, 72, 73, 74, 75], [76, 77, 78, 79, 80], [81, 82, 83, 84, 85], [86, 87, 88, 89, 90], [91, 92, 93, 94, 95], [96, 97, 98, 99, 100], [101, 102, 103, 104, 105], [106, 107, 108, 109, 110], [111, 112, 113, 114, 115], [116, 117, 118, 119, 120], [121, 122, 123, 124, 125], [126, 127, 128, 129, 130], [131, 132, 133, 134, 135], [136, 137, 138, 139, 140], [141, 142, 143, 144, 145], [146, 147, 148, 149, 150], [151, 152, 153, 154, 155], [156, 157, 158, 159, 160], [161, 162, 163, 164, 165], [166, 167, 168, 169, 170], [171, 172, 173, 174, 175], [176, 177, 178, 179, 180], [181, 182, 183, 184, 185], [186, 187, 188, 189, 190], [191, 192, 193, 194, 195], [196, 197, 198, 199, 200], [201, 202, 203, 204, 205], [206, 207, 208, 209, 210], [211, 212, 213, 214, 215], [216, 217, 218, 219, 220], [221, 222, 223, 224, 225], [226, 227, 228, 229, 230], [231, 232, 233, 234, 235], [236, 237, 238, 239, 240], [241, 242, 243, 244, 245], [246, 247, 248, 249, 250], [251, 252, 253, 254, 255]]);

}
translate(v=[0, 0, 2]) {
linear_extrude(height=5) {
union() {
polygon([[119.9620436791635, -10.0], [119.88614853201763, -9.998847719777999], [53.880686985647216, -7.994126032720432], [53.646495296320076, -7.975973004726603], [-5.810086836473021, -0.5439002381274649], [-6.047487665291121, -0.5025204617148387], [-6.279801550623147, -0.4384759607689326], [-6.504869964194179, -0.3523618003068363], [-6.720601698525187, -0.2449781040489396], [-6.9249922972416, -0.11732262012514494], [-7.116142679340018, 0.029418549432351115], [-7.292276784366992, 0.19388196927341883], [-7.451758074560958, 0.3745395389945354], [-7.593104740628792, 0.569712691377185], [-7.71500346987358, 0.7775879886781831], [-7.816321648748018, 0.9962339720600868], [-7.896117886454252, 1.2236191076063734], [-7.953650761810862, 1.45763066217724], [-7.988385712116106, 1.69609433372233], [-8.0, 1.9367944536567043], [-8.000000000000002, 99.39375], [-7.999999999999999, 126.83538329329558], [-7.988630737664156, 127.07353671349598], [-7.954626358757477, 127.30952403072804], [-7.898296147043448, 127.54119884361772], [-7.820152448885596, 127.76645397478553], [-7.720906013247321, 127.98324063648849], [-7.601459527138758, 128.18958706518433], [-7.462899405308439, 128.38361645552916], [-7.306485908855863, 128.56356403069117], [-7.133641682640258, 128.72779309371944], [-6.945938815742489, 128.87480991397337], [-6.745084542670518, 129.00327731321514], [-6.532905715361807, 129.11202682779387], [-6.311332187216184, 129.2000693363015], [-6.082379260288182, 129.26660405603724], [-5.848129355288844, 129.31102582645462], [-5.610713071115836, 129.33293061334462], [143.51094867944454, 135.94330272112006], [143.7578335033689, 135.94204409706296], [144.00339029973705, 135.9164401876724], [144.2452242532848, 135.86674069743202], [144.48097685611515, 135.79343032519606], [144.70834890926406, 135.69722403711918], [144.9251229458497, 135.57906009388333], [145.1291848571225, 135.44009090022388], [145.3185445105055, 135.2816717659965], [145.49135515854522, 135.10534768839287], [145.6459314494865, 134.91283828421348], [145.78076586382062, 134.70602101914633], [145.89454341650796, 134.48691289761004], [145.98615448149076, 134.25765079173254], [146.05470561342344, 134.02047060130883], [165.9330438628631, 49.86597310114771], [165.98320454827606, 49.58055907861434], [166.00000000000003, 49.291257900909926], [166.0, -6.398002531138397], [165.98859115294965, -6.63656923766047], [165.95446874123138, -6.872958527329727], [165.89794420274623, -7.105012856746026], [165.81953344134553, -7.3306142480280165], [165.7199521181364, -7.5477036197617124], [165.60010911958736, -7.754299580396419], [165.46109826205074, -7.9485165125592525], [165.30418830841614, -8.128581783231304], [165.13081138801294, -8.29285192270683], [164.9425499254547, -8.439827624668856], [164.7411221977268, -8.56816743047434], [164.52836665133918, -8.676699972751353], [164.3062251226821, -8.764434666560037], [164.07672511473476, -8.830570750538252], [163.8419612918881, -8.874504595512704], [163.60407636178044, -8.895835213869276], [137.156137109102, -9.99783268273088], [137.05206074732155, -10.0], [119.9620436791635, -10.0], [34.87156720064472, 125.08274924334616], [34.96062665966282, 124.44374999999998], [-3.000000000000001, 124.44374999999998], [-3.0000000000000013, 99.39375], [16.050000000000004, 99.39375], [16.04999999999999, 86.34375], [-3.0, 86.34375], [-3.0000000000000004, 4.143750000000001], [35.10000000000001, 4.143750000000001], [35.100000000000016, -0.6187499999999999], [54.15, -0.6187499999999999], [54.15000000000001, -3.0000000000000013], [79.2, -3.0000000000000013], [79.2, -0.6187499999999999], [98.25000000000001, -0.6187499999999998], [98.25, 1.762500000000001], [117.3, 1.7625000000000017], [117.29999999999998, 4.143749999999999], [136.35000000000002, 4.143750000000002], [136.35000000000005, 24.19375], [136.35000000000005, 65.79526581498008], [152.6303501951956, 68.66593080977538], [149.14870423297376, 88.41132625767018], [145.84070644841873, 107.17191395255269], [141.664467775529, 130.85654041249649], [116.66854633478026, 127.10921194740828], [116.86608588567066, 126.48391660740211], [98.23444586769057, 123.19865577738476], [101.71609182991254, 103.45326032948991], [105.1528387505238, 83.96250000000003], [92.24999999999987, 83.96250000000003], [92.25, 81.58124999999998], [73.19999999999963, 81.58125000000001], [73.20000000000002, 79.19999999999996], [60.149999999999984, 79.19999999999996], [60.149999999999764, 81.58125000000003], [41.100000000000016, 81.58125000000001], [41.100000000000016, 99.39375000000001], [60.149999999999984, 99.39375], [60.14999999999999, 124.44375], [34.87156720064472, 125.08274924334616]], [[0, 1, 2, 3, 4, 5, 6, 7, 8, 9, 10, 11, 12, 13, 14, 15, 16, 17, 18, 19, 20, 21, 22, 23, 24, 25, 26, 27, 28, 29, 30, 31, 32, 33, 34, 35, 36, 37, 38, 39, 40, 41, 42, 43, 44, 45, 46, 47, 48, 49, 50, 51, 52, 53, 54, 55, 56, 57, 58, 59, 60, 61, 62, 63, 64, 65, 66, 67, 68, 69, 70, 71, 72, 73, 74, 75], [76, 77, 78, 79, 80, 81, 82, 83, 84, 85, 86, 87, 88, 89, 90, 91, 92, 93, 94, 95, 96, 97, 98, 99, 100, 101, 102, 103, 104, 105, 106, 107, 108, 109, 110, 111, 112, 113, 114, 115, 116]]);

polygon([[117.29999999999997, 80.0455395898675], [123.91558021508602, 80.20612383586537], [124.8785755520589, 81.7968652027765], [125.15376661456881, 80.23617913304282], [130.55645011989614, 80.36732195481524], [125.36267357887374, 79.05140886438873], [127.43586606663155, 67.29374999999999], [117.30000000000004, 67.29374999999997], [117.29999999999997, 80.0455395898675]], [[0, 1, 2, 3, 4, 5, 6, 7, 8]]);

}
}
}
}}
